PJ-Verweij/LowCostHighPrecisionPositioning---BASE2-ROVER2/SolidWorks 3D models/BASE2/Solarpanel/Base.B.solarpanel_victron_20watt.SLDASM

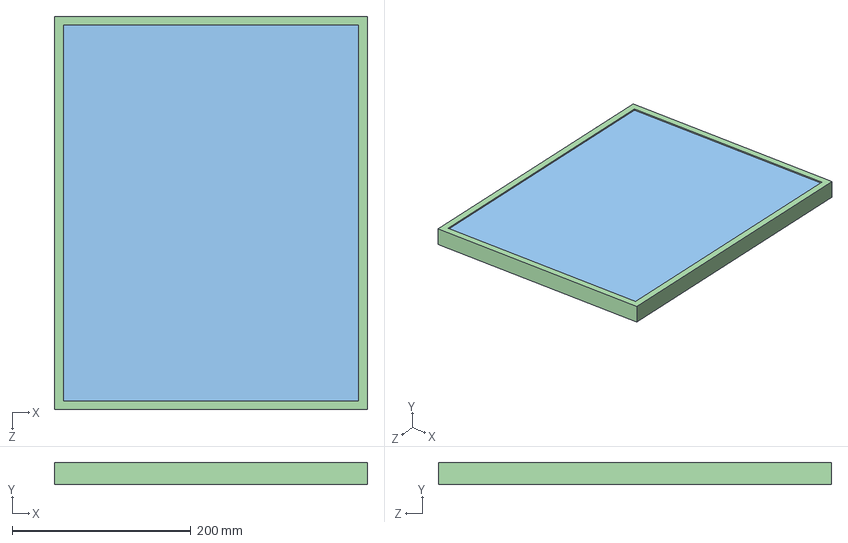
[picture p10: CAD file, 2020-09-22]
SolidWorks 3D models/BASE2/Solarpanel/Base.B.solarpanel_victron_20watt.SLDASM
350.0 x 25.0 x 440.0 mm
Solarpanel.sides
Solarpanel.glass
Solarpanel.cells
Solarpanel.backplate
