PJ-Verweij/LowCostHighPrecisionPositioning---BASE2-ROVER2/SolidWorks 3D models/BASE2/Base.Leg.Assembly.SLDASM

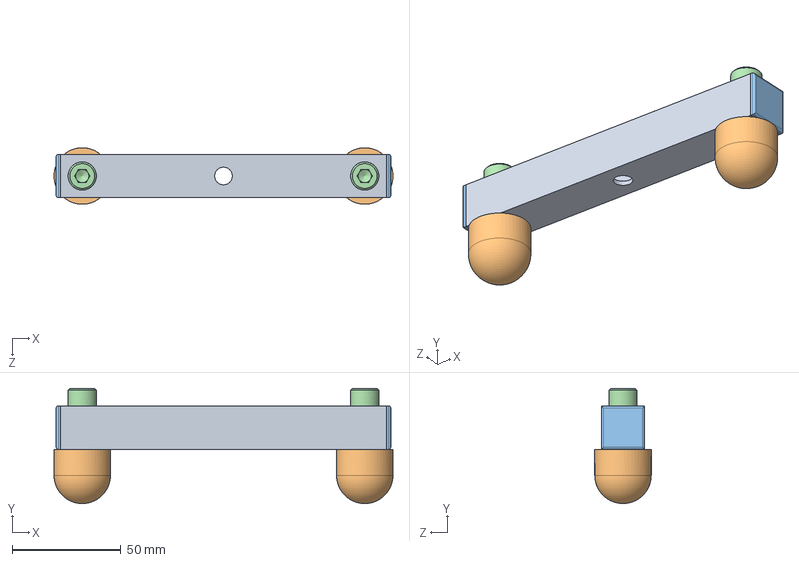
[picture p16: CAD file, 2020-09-22]
SolidWorks 3D models/BASE2/Base.Leg.Assembly.SLDASM
156.0 x 53.0 x 26.0 mm
Base.M.Square_Tube_150x20x20
Base.B.Rubber_Feet x 2
Base.B.Square_Tube_Cap x 2
socket head cap screw_am x 2
