PJ-Verweij/LowCostHighPrecisionPositioning---BASE2-ROVER2/SolidWorks 3D models/BASE2/Base.Cap.Assembly.SLDASM

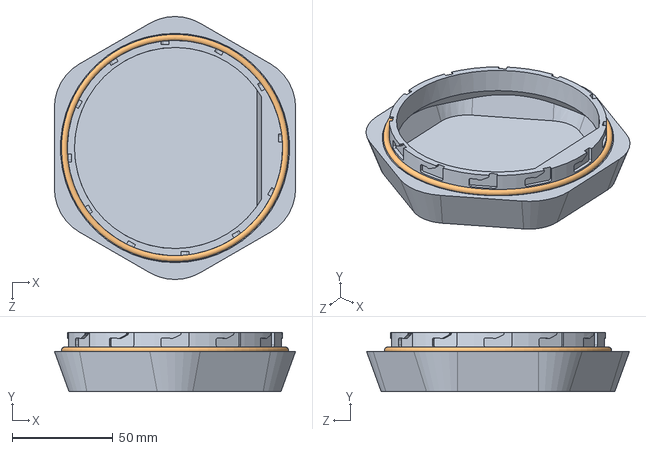
[picture p17: CAD file, 2020-09-22]
SolidWorks 3D models/BASE2/Base.Cap.Assembly.SLDASM
120.0 x 29.5 x 130.8 mm
Base.M.cap
Base.B.3x106_o-ring
