PJ-Verweij/LowCostHighPrecisionPositioning---BASE2-ROVER2/SolidWorks 3D models/BASE2/Base.Solarconnectorcap.Assembly.SLDASM

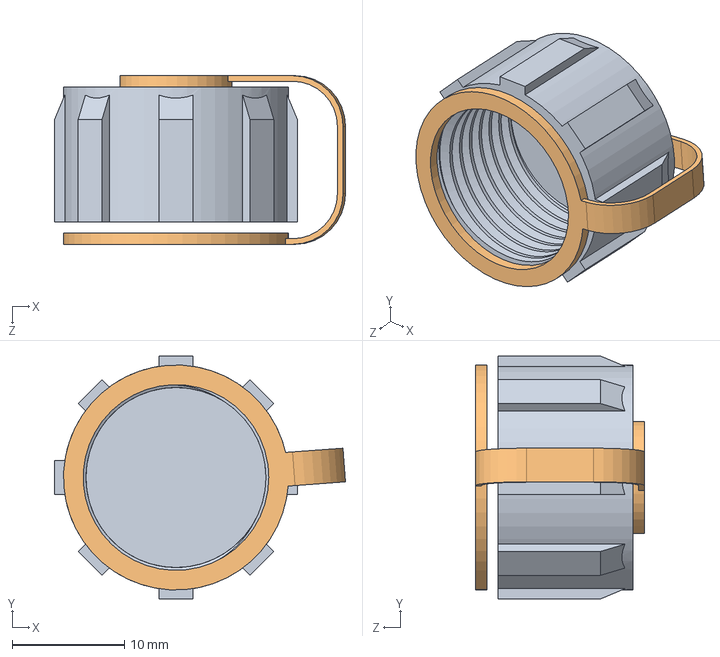
[picture p18: CAD file, 2020-09-22]
SolidWorks 3D models/BASE2/Base.Solarconnectorcap.Assembly.SLDASM
25.9 x 21.6 x 15.0 mm
Base.B.solarconnector_cap
Base.B.solarconnector_lip
