PJ-Verweij/LowCostHighPrecisionPositioning---BASE2-ROVER2/SolidWorks 3D models/BASE2/Base.B.cn3772_MPPT_regulator.SLDPRT

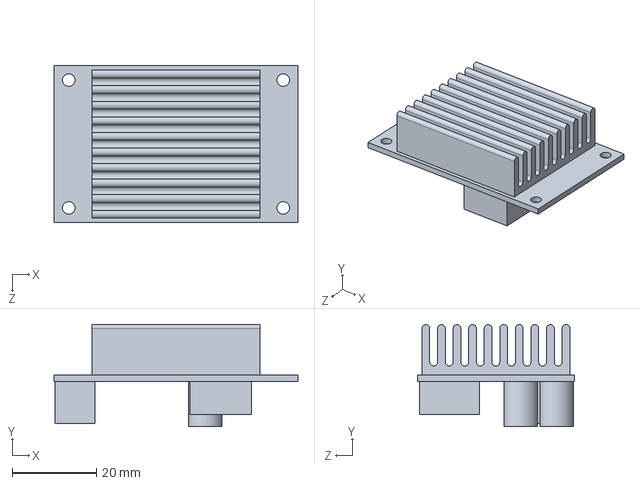
[picture p19: CAD file, 2020-09-22]
SolidWorks 3D models/BASE2/Base.B.cn3772_MPPT_regulator.SLDPRT
58.0 x 24.2 x 37.4 mm
