PJ-Verweij/LowCostHighPrecisionPositioning---BASE2-ROVER2/SolidWorks 3D models/BASE2/Solarpanel/Base.M.example_solarpanel_stand.SLDPRT

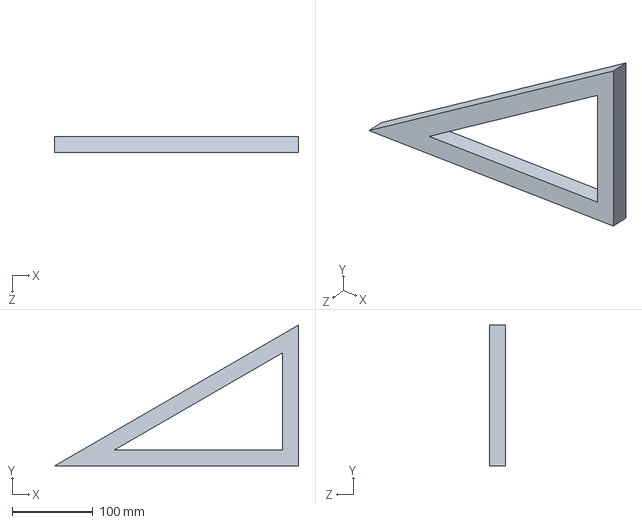
[picture p20: CAD file, 2020-09-22]
SolidWorks 3D models/BASE2/Solarpanel/Base.M.example_solarpanel_stand.SLDPRT
303.1 x 175.0 x 20.0 mm
