PJ-Verweij/LowCostHighPrecisionPositioning---BASE2-ROVER2/SolidWorks 3D models/ROVER2/Phoneholder/Rover.B.spring.SLDPRT

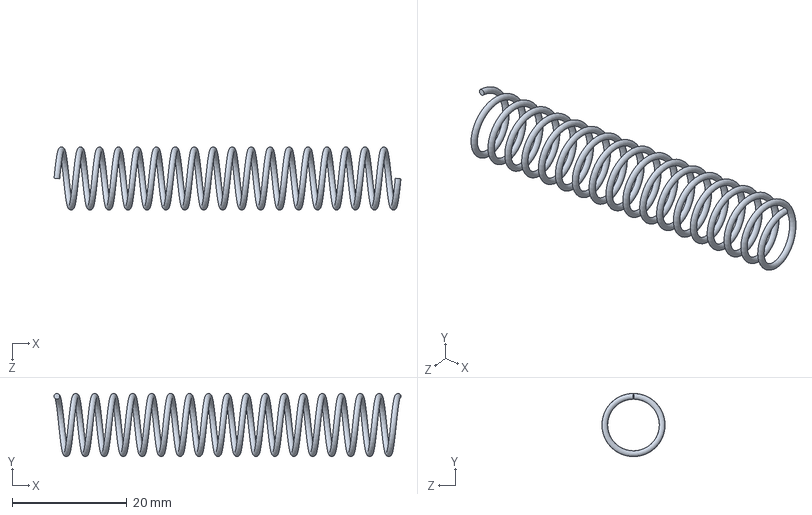
[picture p21: CAD file, 2020-09-22]
SolidWorks 3D models/ROVER2/Phoneholder/Rover.B.spring.SLDPRT
60.4 x 11.0 x 11.0 mm
