PJ-Verweij/LowCostHighPrecisionPositioning---BASE2-ROVER2/SolidWorks 3D models/ROVER2/Rover.B.18650x2_holder.SLDPRT

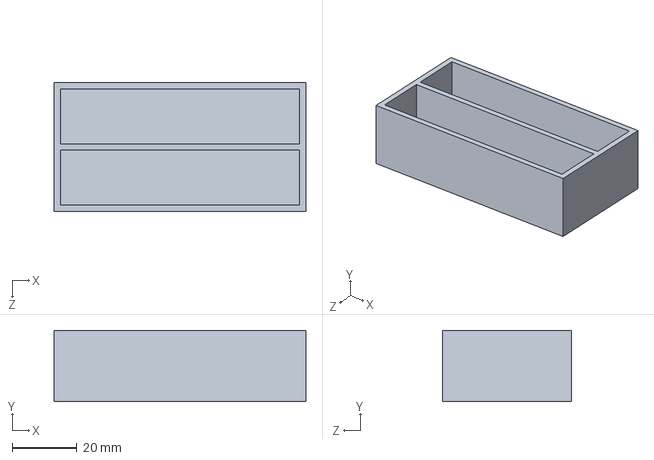
[picture p22: CAD file, 2020-09-22]
SolidWorks 3D models/ROVER2/Rover.B.18650x2_holder.SLDPRT
78.0 x 22.0 x 40.0 mm
