PJ-Verweij/LowCostHighPrecisionPositioning---BASE2-ROVER2/SolidWorks 3D models/shared parts ROVER2 and BASE2/Universal.B.Insert.5x5xm3.SLDPRT

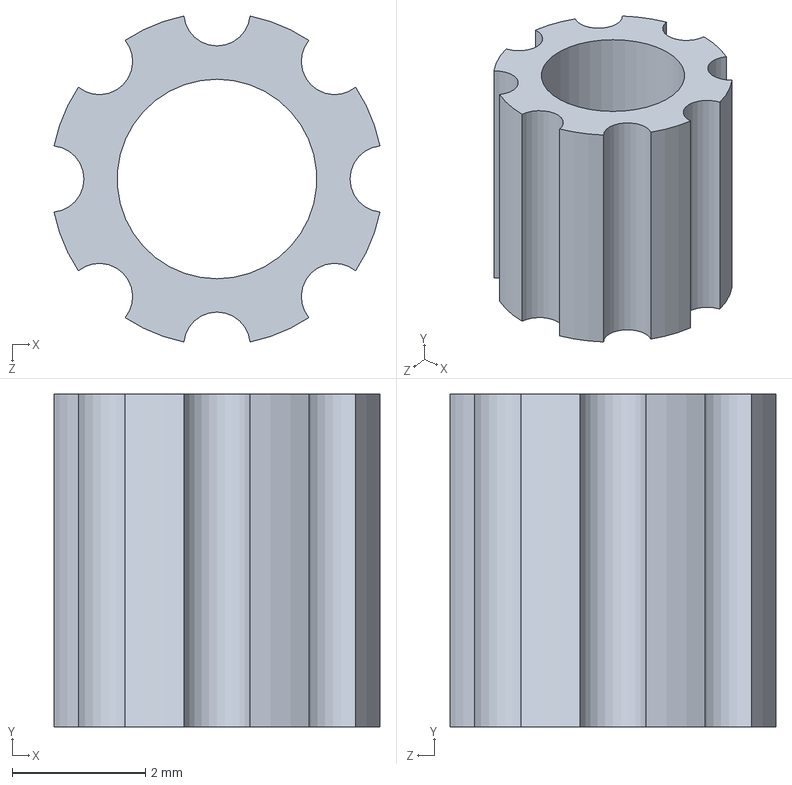
[picture p23: CAD file, 2020-09-22]
SolidWorks 3D models/shared parts ROVER2 and BASE2/Universal.B.Insert.5x5xm3.SLDPRT
4.90 x 5.00 x 4.90 mm
