PJ-Verweij/LowCostHighPrecisionPositioning---BASE2-ROVER2/SolidWorks 3D models/BASE2/Antennatop/Base.B.cellular_antenna.SLDPRT

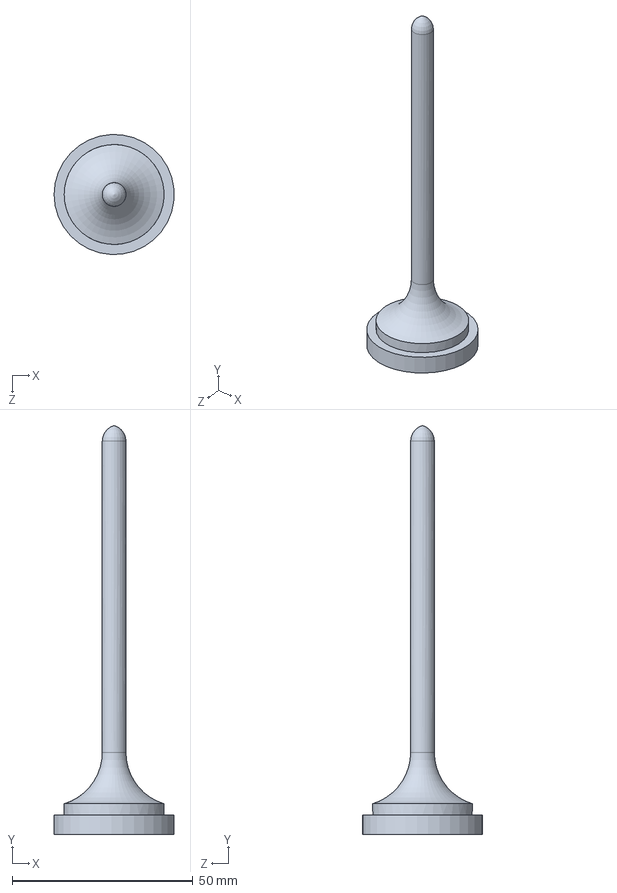
[picture p24: CAD file, 2020-09-22]
SolidWorks 3D models/BASE2/Antennatop/Base.B.cellular_antenna.SLDPRT
33.1 x 113.0 x 33.2 mm
