PJ-Verweij/LowCostHighPrecisionPositioning---BASE2-ROVER2/SolidWorks 3D models/BASE2/Base.B.solarconnector_turnablecap.SLDPRT

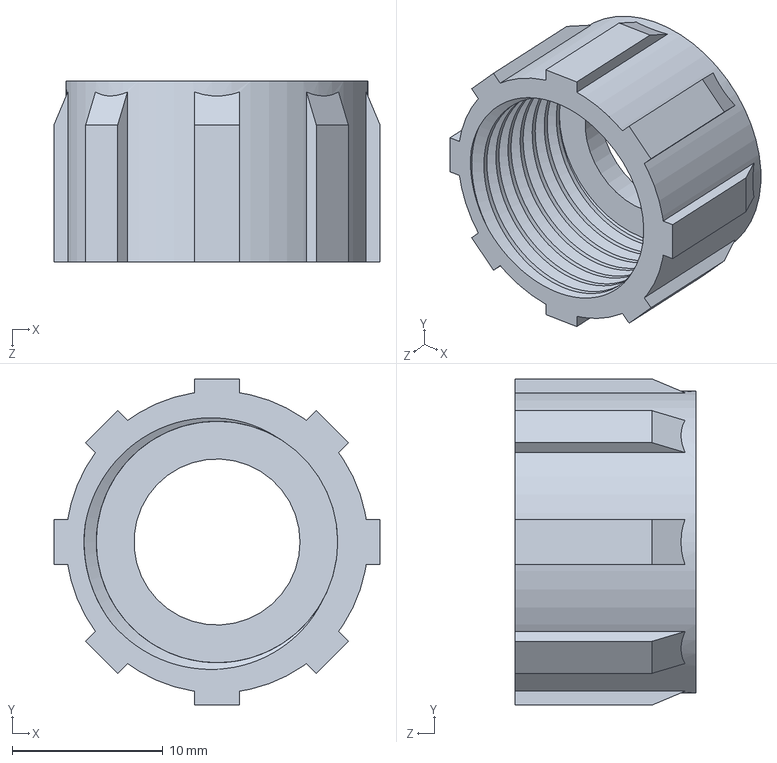
[picture p25: CAD file, 2020-09-22]
SolidWorks 3D models/BASE2/Base.B.solarconnector_turnablecap.SLDPRT
21.6 x 21.6 x 12.0 mm
