PJ-Verweij/LowCostHighPrecisionPositioning---BASE2-ROVER2/SolidWorks 3D models/BASE2/Solarpanel/Solarpanel.backplate.SLDPRT

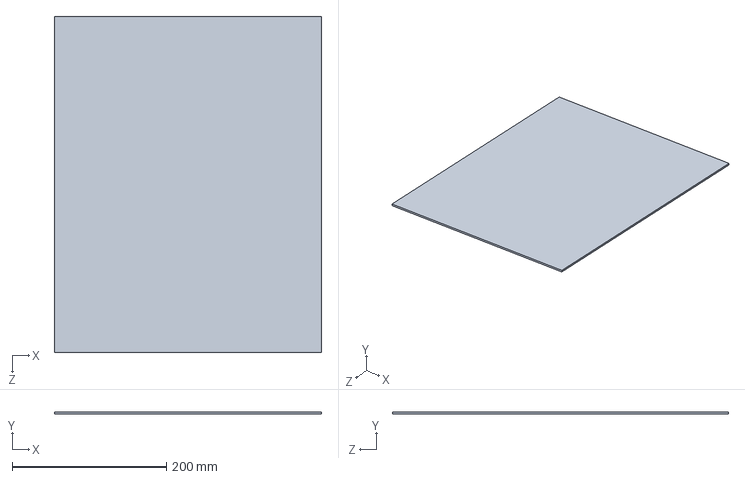
[picture p26: CAD file, 2020-09-22]
SolidWorks 3D models/BASE2/Solarpanel/Solarpanel.backplate.SLDPRT
346.0 x 3.00 x 436.0 mm
