PJ-Verweij/LowCostHighPrecisionPositioning---BASE2-ROVER2/SolidWorks 3D models/BASE2/Tripodclamp/Base.M.fixed_tripod_coupler.SLDPRT

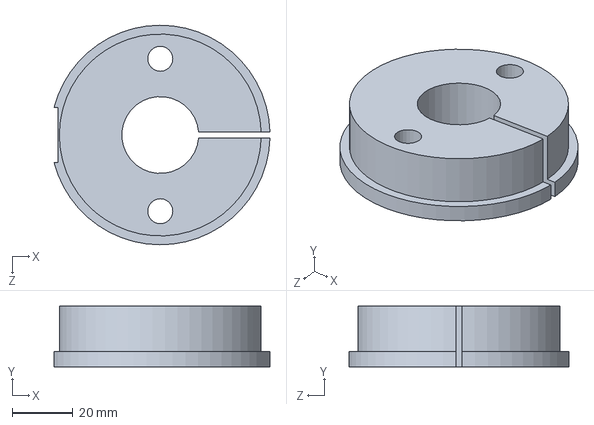
[picture p27: CAD file, 2020-09-22]
SolidWorks 3D models/BASE2/Tripodclamp/Base.M.fixed_tripod_coupler.SLDPRT
70.8 x 20.0 x 72.0 mm
