PJ-Verweij/LowCostHighPrecisionPositioning---BASE2-ROVER2/SolidWorks 3D models/ROVER2/Phoneholder/telefoonhouderbase.STL

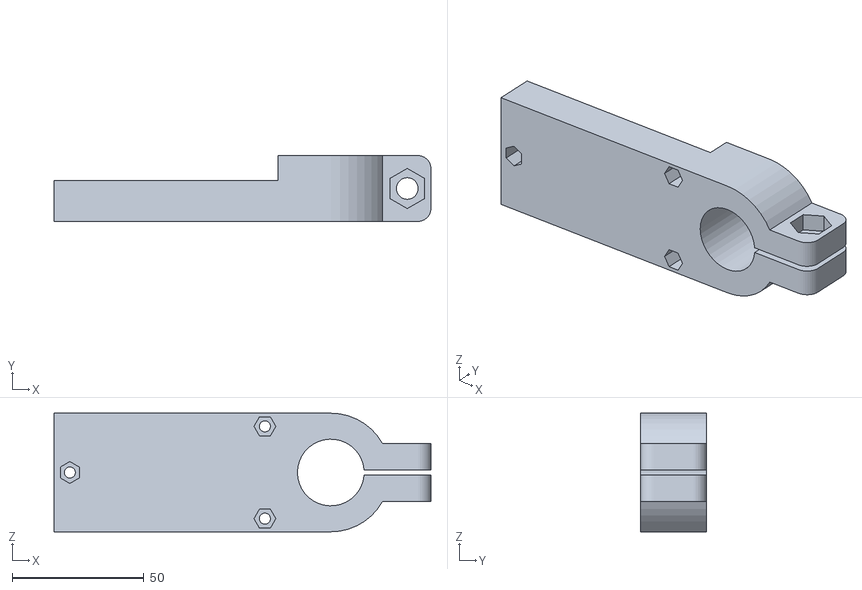
[picture p28: CAD file, 2020-09-22]
SolidWorks 3D models/ROVER2/Phoneholder/telefoonhouderbase.STL
143.0 x 25.0 x 45.0
