PJ-Verweij/LowCostHighPrecisionPositioning---BASE2-ROVER2/SolidWorks 3D models/ROVER2/Rover.M.BatteryPCB.SLDPRT

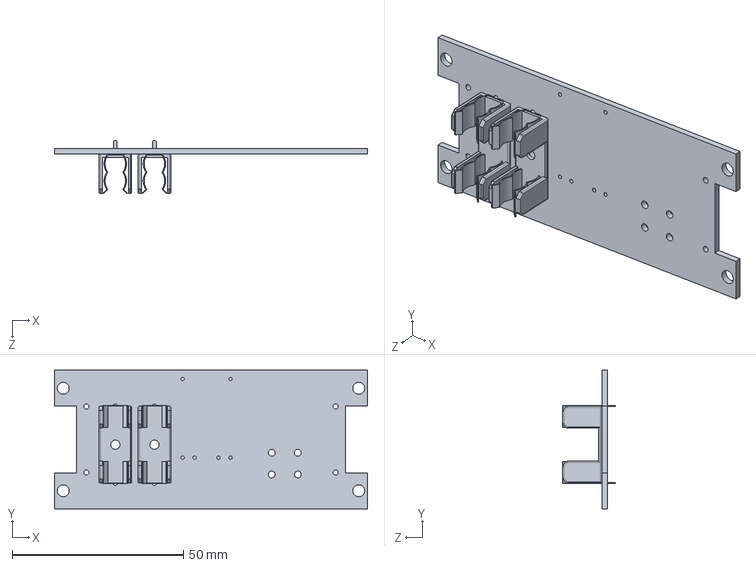
[picture p29: CAD file, 2020-09-22]
SolidWorks 3D models/ROVER2/Rover.M.BatteryPCB.SLDPRT
91.5 x 40.5 x 15.5 mm
