PJ-Verweij/LowCostHighPrecisionPositioning---BASE2-ROVER2/SolidWorks 3D models/ROVER2/Tripodclamp/Rover.M.open_tripod_coupler.SLDPRT

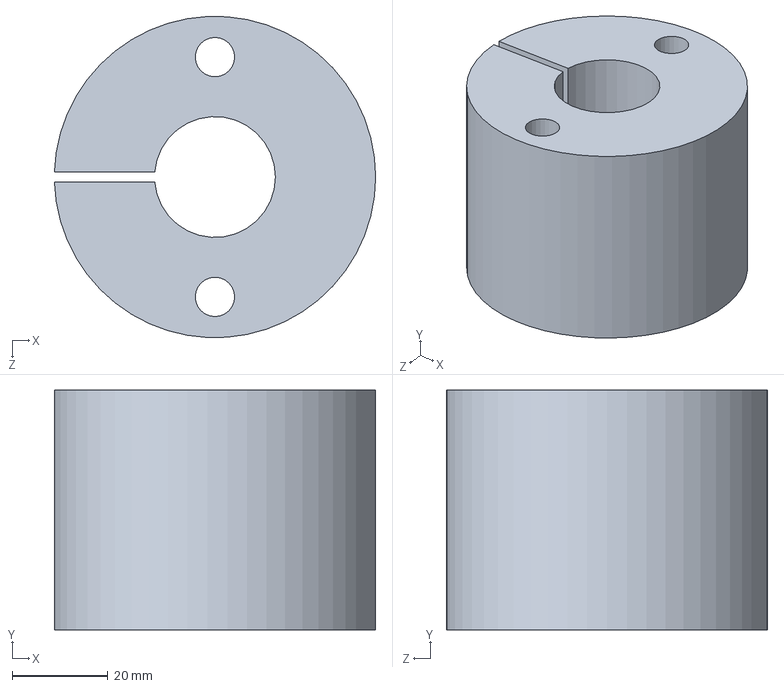
[picture p30: CAD file, 2020-09-22]
SolidWorks 3D models/ROVER2/Tripodclamp/Rover.M.open_tripod_coupler.SLDPRT
67.0 x 50.0 x 66.9 mm
