PJ-Verweij/LowCostHighPrecisionPositioning---BASE2-ROVER2/SolidWorks 3D models/shared parts ROVER2 and BASE2/Tripod/Tripodleg.hinge.SLDPRT

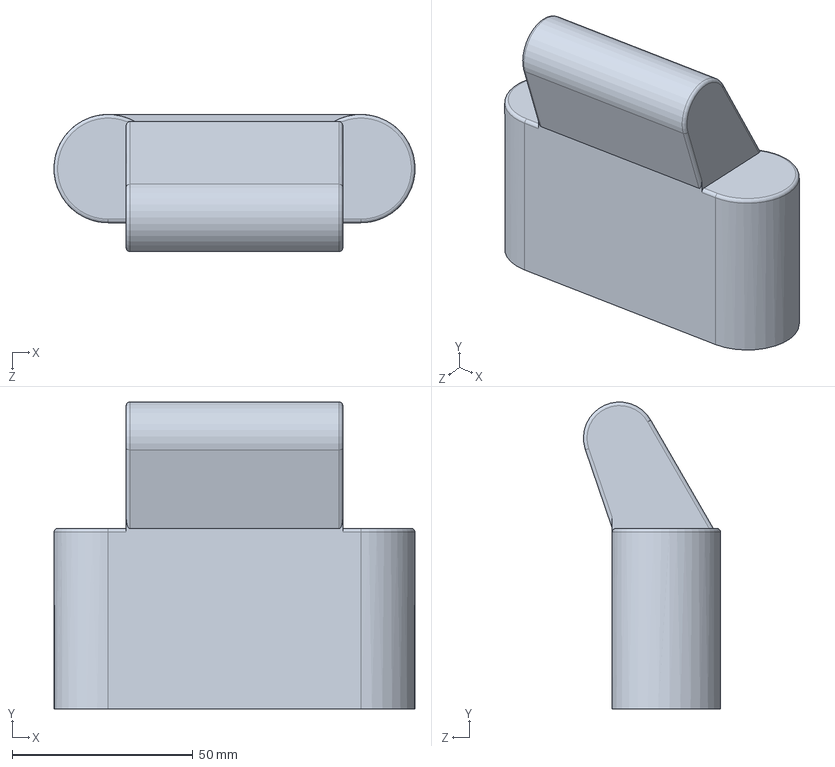
[picture p31: CAD file, 2020-09-22]
SolidWorks 3D models/shared parts ROVER2 and BASE2/Tripod/Tripodleg.hinge.SLDPRT
100.0 x 85.0 x 38.0 mm
