PJ-Verweij/LowCostHighPrecisionPositioning---BASE2-ROVER2/SolidWorks 3D models/shared parts ROVER2 and BASE2/Universal.B.knob_m8.SLDPRT

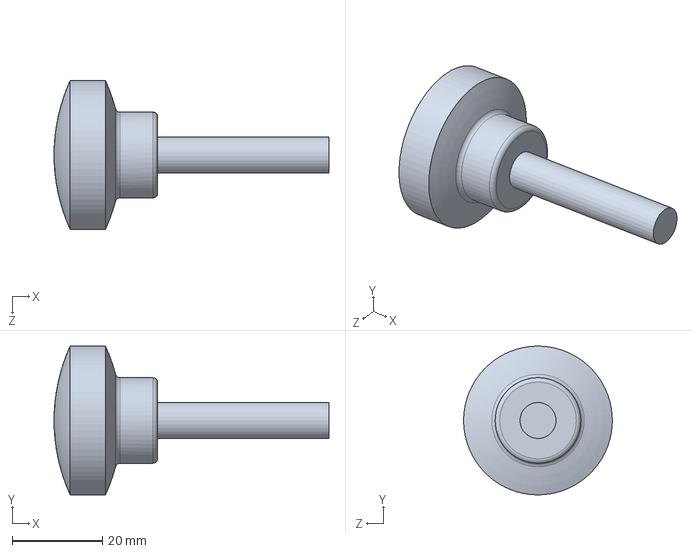
[picture p32: CAD file, 2020-09-22]
SolidWorks 3D models/shared parts ROVER2 and BASE2/Universal.B.knob_m8.SLDPRT
61.0 x 33.0 x 33.0 mm
