PJ-Verweij/LowCostHighPrecisionPositioning---BASE2-ROVER2/SolidWorks 3D models/BASE2/Antennatop/Base.M.Antennatop.SLDPRT

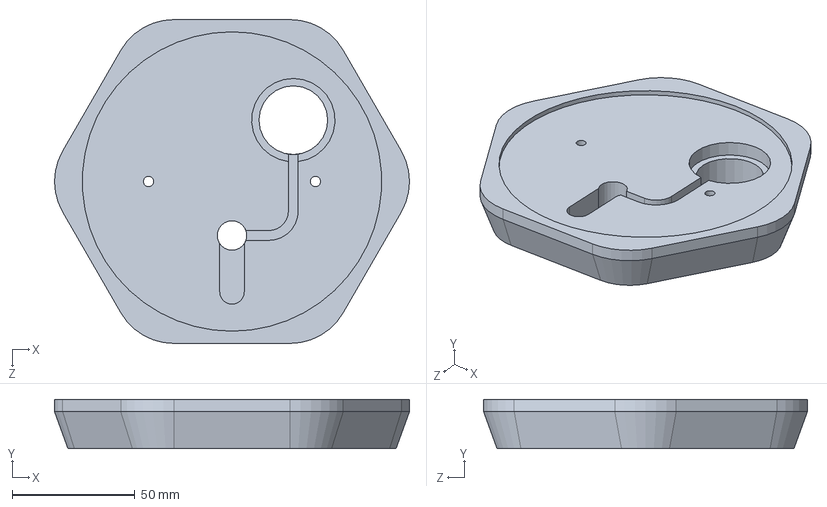
[picture p33: CAD file, 2020-09-22]
SolidWorks 3D models/BASE2/Antennatop/Base.M.Antennatop.SLDPRT
144.7 x 20.0 x 132.0 mm
