PJ-Verweij/LowCostHighPrecisionPositioning---BASE2-ROVER2/SolidWorks 3D models/BASE2/Base.B.Rubber_Feet.SLDPRT

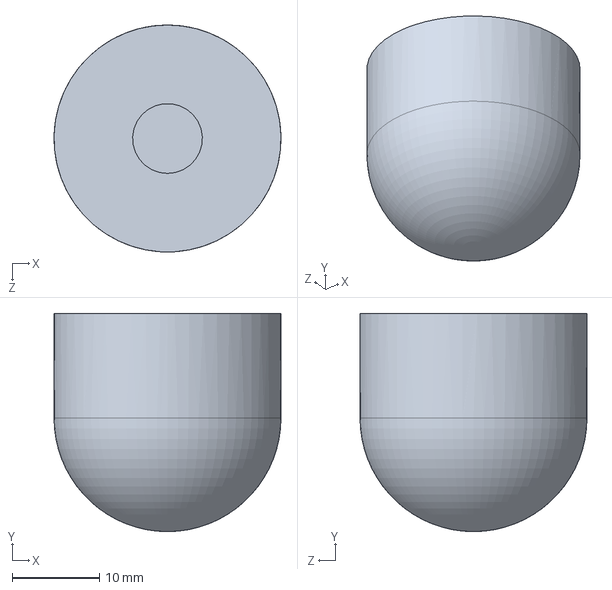
[picture p34: CAD file, 2020-09-22]
SolidWorks 3D models/BASE2/Base.B.Rubber_Feet.SLDPRT
26.0 x 25.0 x 26.0 mm
