PJ-Verweij/LowCostHighPrecisionPositioning---BASE2-ROVER2/SolidWorks 3D models/BASE2/Cable-gland-pg7-pg19/Cable Gland PG7-PG19 Body.SLDPRT

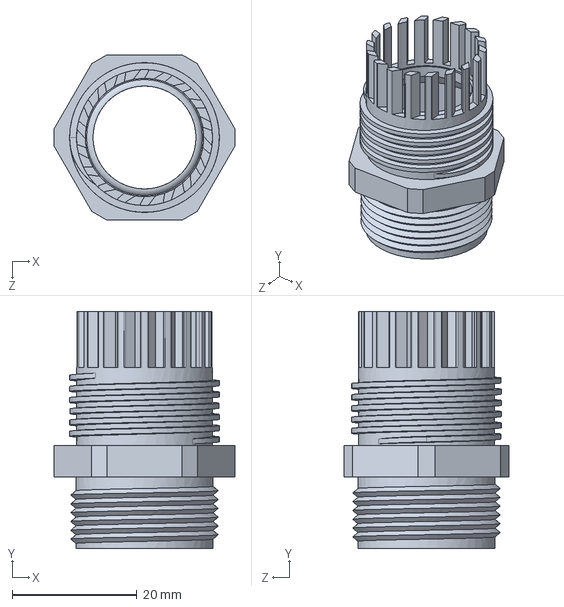
[picture p35: CAD file, 2020-09-22]
SolidWorks 3D models/BASE2/Cable-gland-pg7-pg19/Cable Gland PG7-PG19 Body.SLDPRT
29.0 x 38.0 x 26.5 mm
