PJ-Verweij/LowCostHighPrecisionPositioning---BASE2-ROVER2/SolidWorks 3D models/ROVER2/Phoneholder/Rover.M.Phoneholder_movablepart.SLDPRT

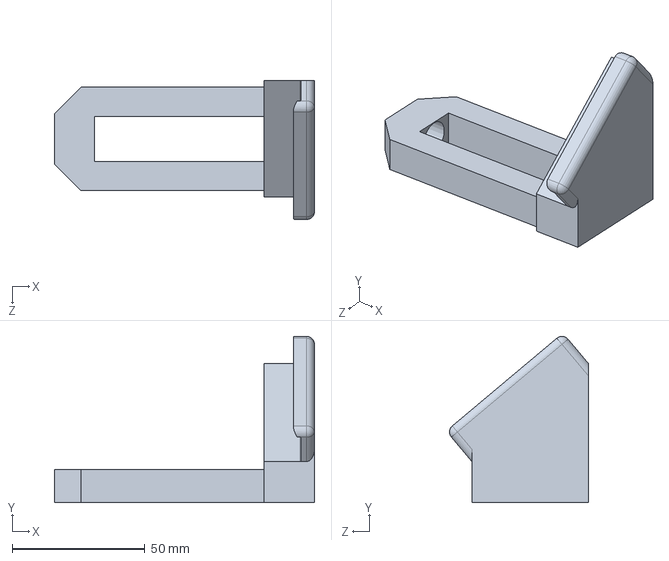
[picture p36: CAD file, 2020-09-22]
SolidWorks 3D models/ROVER2/Phoneholder/Rover.M.Phoneholder_movablepart.SLDPRT
98.0 x 62.7 x 52.4 mm
