PJ-Verweij/LowCostHighPrecisionPositioning---BASE2-ROVER2/SolidWorks 3D models/shared parts ROVER2 and BASE2/Tripod/Tripodleg.feet.SLDPRT

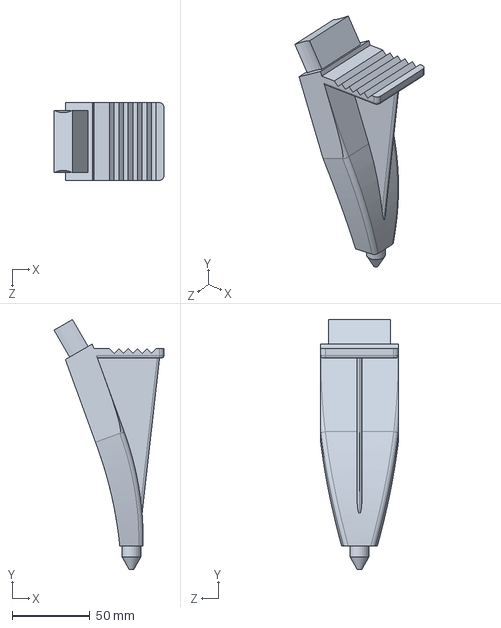
[picture p37: CAD file, 2020-09-22]
SolidWorks 3D models/shared parts ROVER2 and BASE2/Tripod/Tripodleg.feet.SLDPRT
70.7 x 160.7 x 50.0 mm
