PJ-Verweij/LowCostHighPrecisionPositioning---BASE2-ROVER2/SolidWorks 3D models/shared parts ROVER2 and BASE2/Universal.M.poleclamp.SLDPRT

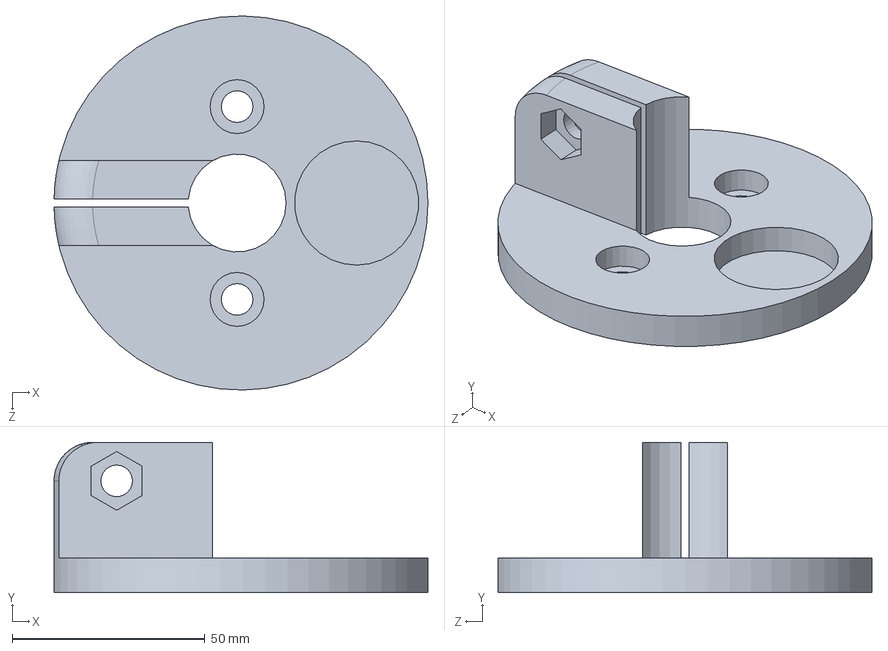
[picture p38: CAD file, 2020-09-22]
SolidWorks 3D models/shared parts ROVER2 and BASE2/Universal.M.poleclamp.SLDPRT
97.0 x 39.0 x 97.0 mm
