PJ-Verweij/LowCostHighPrecisionPositioning---BASE2-ROVER2/SolidWorks 3D models/BASE2/Base.M.Foamblockholder.SLDPRT

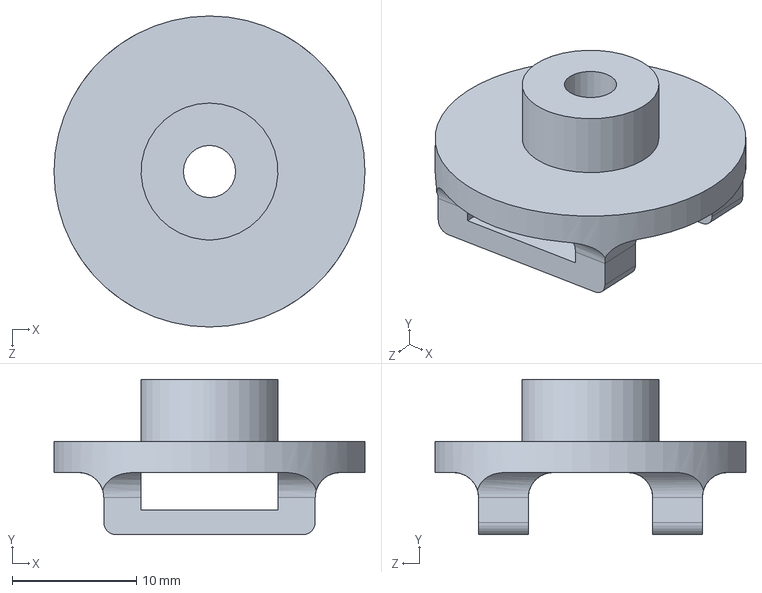
[picture p39: CAD file, 2020-09-22]
SolidWorks 3D models/BASE2/Base.M.Foamblockholder.SLDPRT
25.0 x 12.5 x 25.0 mm
