PJ-Verweij/LowCostHighPrecisionPositioning---BASE2-ROVER2/SolidWorks 3D models/BASE2/Solarpanel/Solarpanel.cells.SLDPRT

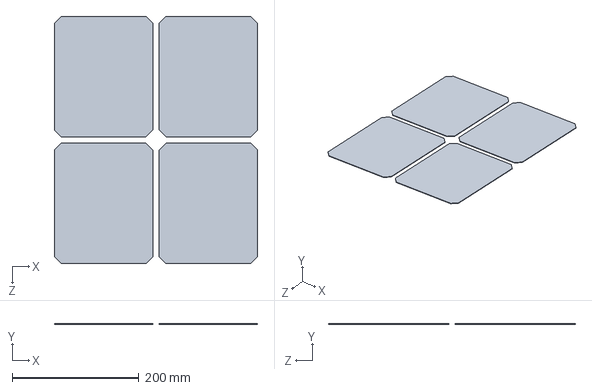
[picture p40: CAD file, 2020-09-22]
SolidWorks 3D models/BASE2/Solarpanel/Solarpanel.cells.SLDPRT
320.0 x 1.00 x 390.0 mm
