PJ-Verweij/LowCostHighPrecisionPositioning---BASE2-ROVER2/SolidWorks 3D models/ROVER2/Cable-gland-pg7-pg19/Cable Gland PG7-PG19 Sleeve.SLDPRT

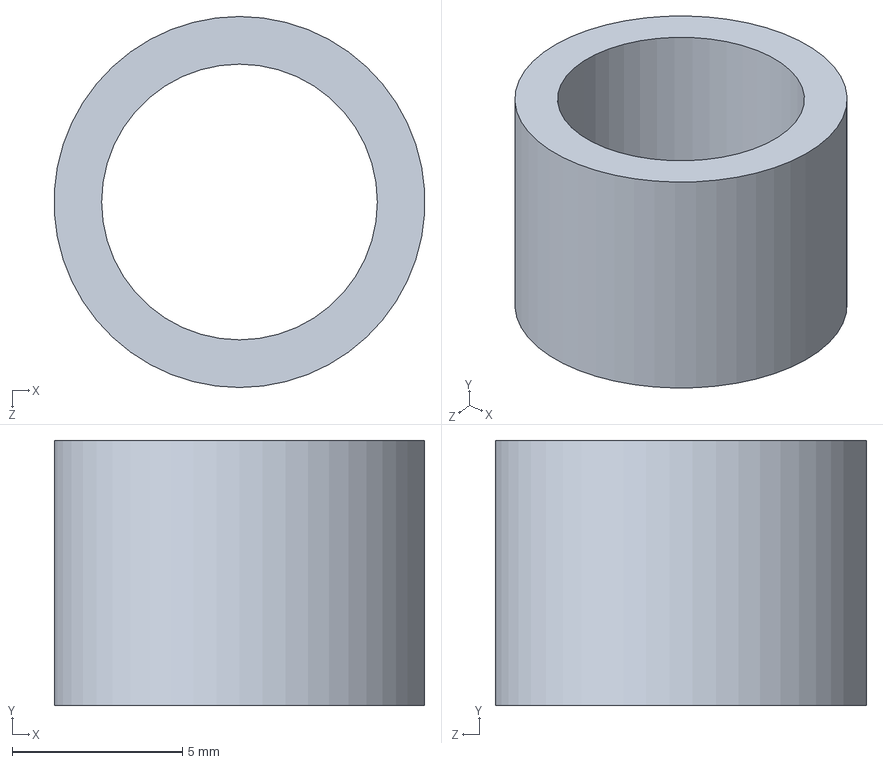
[picture p41: CAD file, 2020-09-22]
SolidWorks 3D models/ROVER2/Cable-gland-pg7-pg19/Cable Gland PG7-PG19 Sleeve.SLDPRT
10.9 x 7.80 x 10.9 mm
