PJ-Verweij/LowCostHighPrecisionPositioning---BASE2-ROVER2/SolidWorks 3D models/ROVER2/Rover.M.Lowerhousing_rubber.SLDPRT

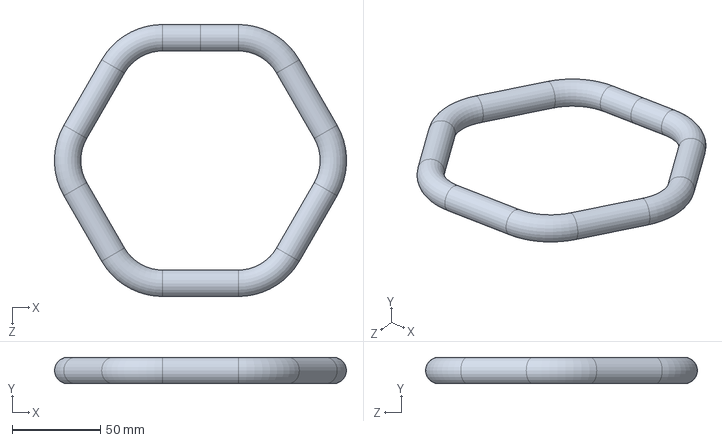
[picture p42: CAD file, 2020-09-22]
SolidWorks 3D models/ROVER2/Rover.M.Lowerhousing_rubber.SLDPRT
165.5 x 15.0 x 154.2 mm
