PJ-Verweij/LowCostHighPrecisionPositioning---BASE2-ROVER2/SolidWorks 3D models/shared parts ROVER2 and BASE2/Tripod/Tripodleg.clampclip.SLDPRT

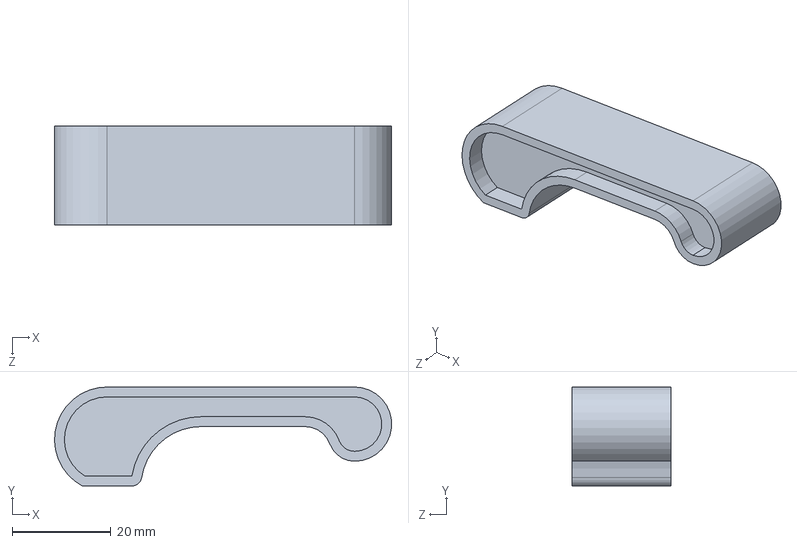
[picture p43: CAD file, 2020-09-22]
SolidWorks 3D models/shared parts ROVER2 and BASE2/Tripod/Tripodleg.clampclip.SLDPRT
68.1 x 20.0 x 20.0 mm
