PJ-Verweij/LowCostHighPrecisionPositioning---BASE2-ROVER2/SolidWorks 3D models/shared parts ROVER2 and BASE2/Universal.B.XT60E-M.SLDPRT

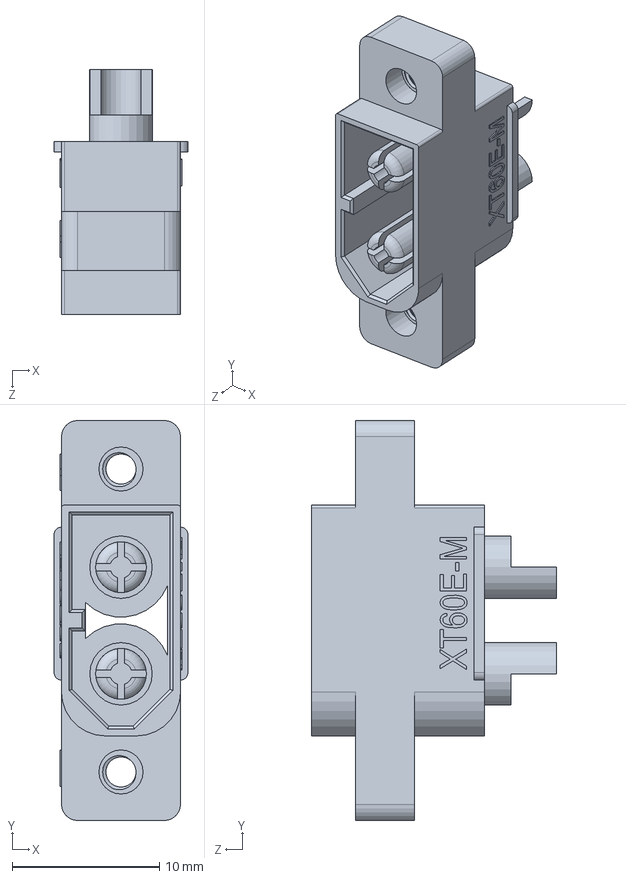
[picture p44: CAD file, 2020-09-22]
SolidWorks 3D models/shared parts ROVER2 and BASE2/Universal.B.XT60E-M.SLDPRT
9.10 x 27.2 x 16.6 mm
