PJ-Verweij/LowCostHighPrecisionPositioning---BASE2-ROVER2/SolidWorks 3D models/BASE2/Antennatop/thread adapter antenna top.SLDPRT

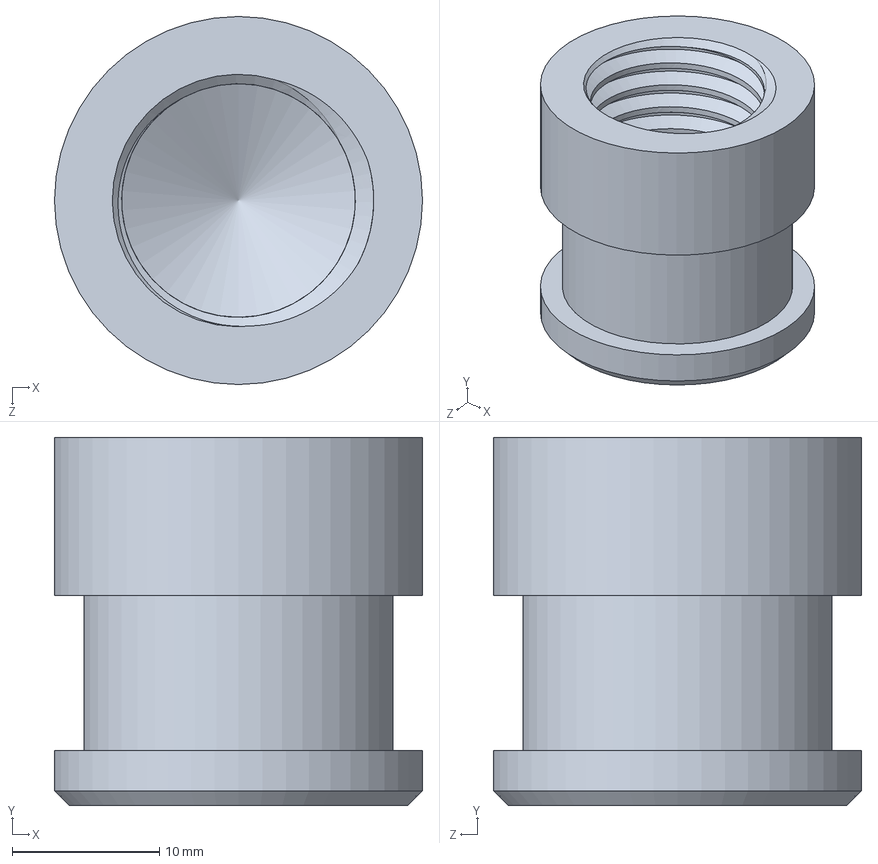
[picture p45: CAD file, 2020-09-22]
SolidWorks 3D models/BASE2/Antennatop/thread adapter antenna top.SLDPRT
25.0 x 25.0 x 25.0 mm
