PJ-Verweij/LowCostHighPrecisionPositioning---BASE2-ROVER2/SolidWorks 3D models/BASE2/Base.M.cap.SLDPRT

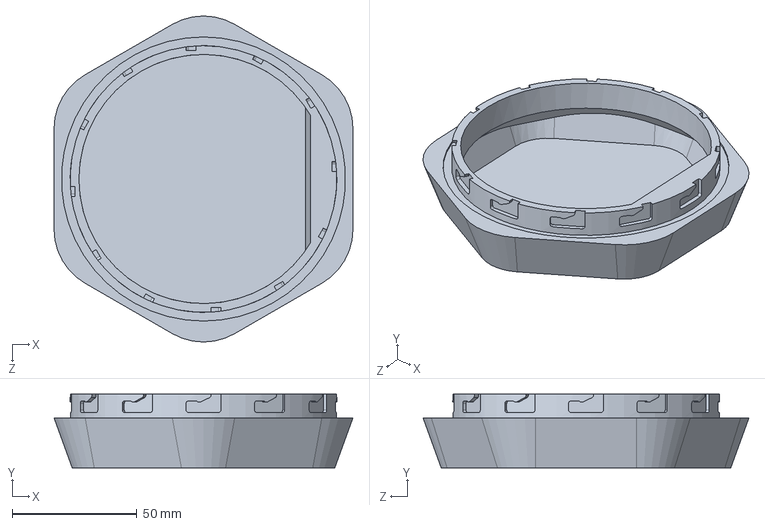
[picture p46: CAD file, 2020-09-22]
SolidWorks 3D models/BASE2/Base.M.cap.SLDPRT
120.0 x 29.5 x 130.8 mm
