PJ-Verweij/LowCostHighPrecisionPositioning---BASE2-ROVER2/SolidWorks 3D models/BASE2/Solarpanel/Solarpanel.sides.SLDPRT

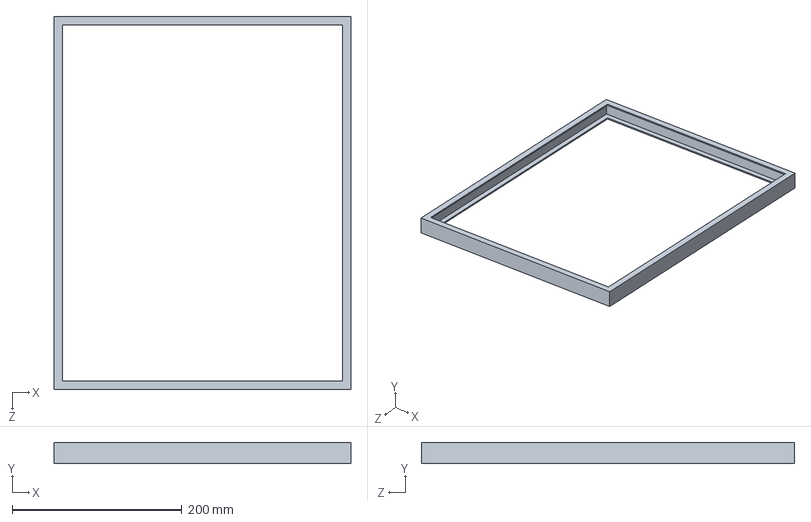
[picture p47: CAD file, 2020-09-22]
SolidWorks 3D models/BASE2/Solarpanel/Solarpanel.sides.SLDPRT
350.0 x 25.0 x 440.0 mm
