PJ-Verweij/LowCostHighPrecisionPositioning---BASE2-ROVER2/SolidWorks 3D models/ROVER2/Phoneholder/Part11.SLDPRT

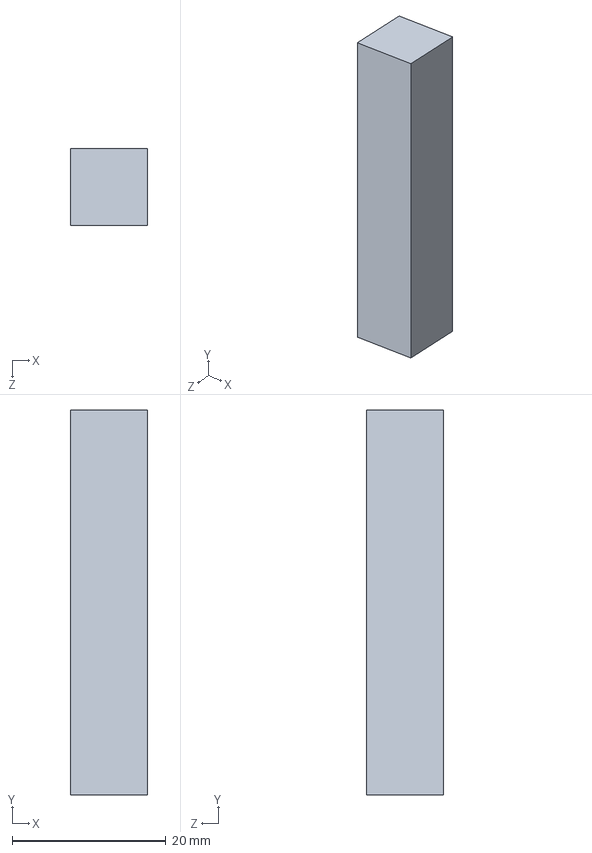
[picture p48: CAD file, 2020-09-22]
SolidWorks 3D models/ROVER2/Phoneholder/Part11.SLDPRT
10.0 x 50.0 x 10.0 mm
