PJ-Verweij/LowCostHighPrecisionPositioning---BASE2-ROVER2/SolidWorks 3D models/ROVER2/Rover.B.regular_usb_breakout.SLDPRT

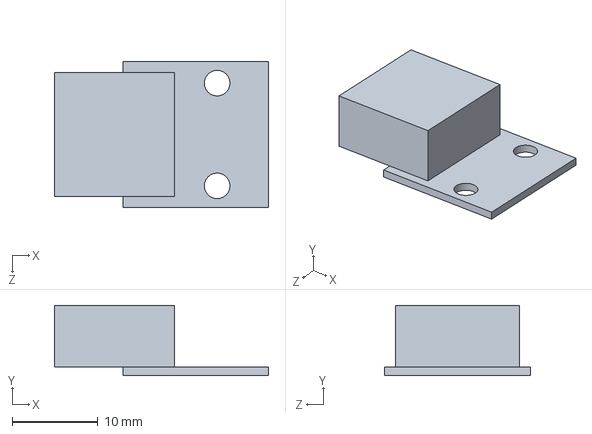
[picture p49: CAD file, 2020-09-22]
SolidWorks 3D models/ROVER2/Rover.B.regular_usb_breakout.SLDPRT
25.0 x 8.20 x 17.0 mm
