PJ-Verweij/LowCostHighPrecisionPositioning---BASE2-ROVER2/SolidWorks 3D models/shared parts ROVER2 and BASE2/Universal.B.level_32mm.SLDPRT

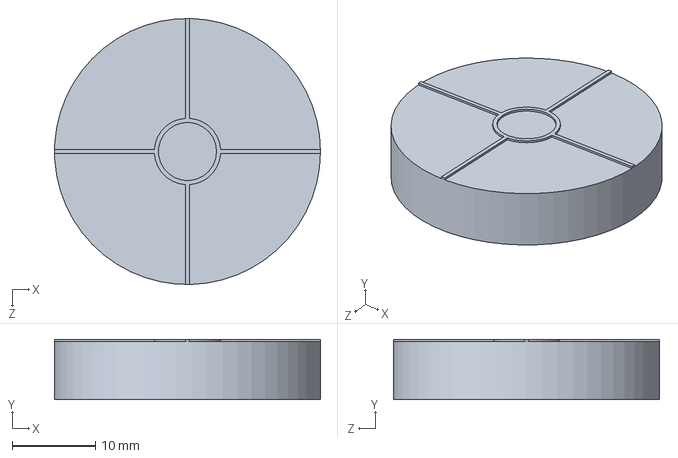
[picture p50: CAD file, 2020-09-22]
SolidWorks 3D models/shared parts ROVER2 and BASE2/Universal.B.level_32mm.SLDPRT
32.0 x 7.25 x 32.0 mm
