PJ-Verweij/LowCostHighPrecisionPositioning---BASE2-ROVER2/SolidWorks 3D models/BASE2/Base.B.solarconnector_cablegland.SLDPRT

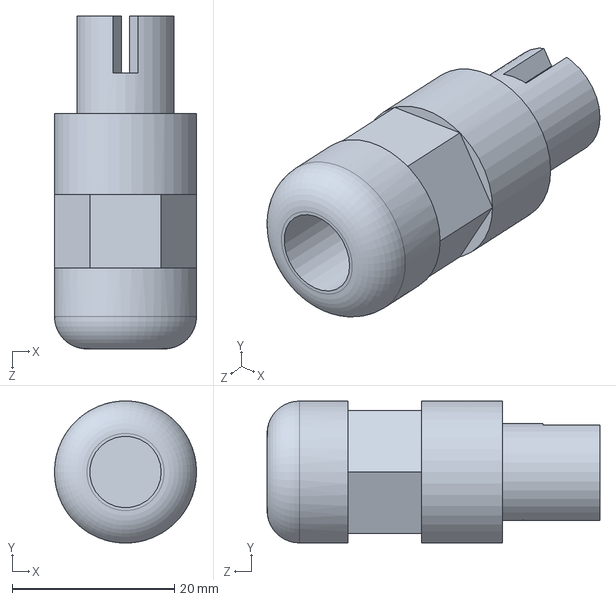
[picture p51: CAD file, 2020-09-22]
SolidWorks 3D models/BASE2/Base.B.solarconnector_cablegland.SLDPRT
17.5 x 17.5 x 41.0 mm
