PJ-Verweij/LowCostHighPrecisionPositioning---BASE2-ROVER2/SolidWorks 3D models/ROVER2/Phoneholder/Rover.M.Phoneholder_toppart.SLDPRT

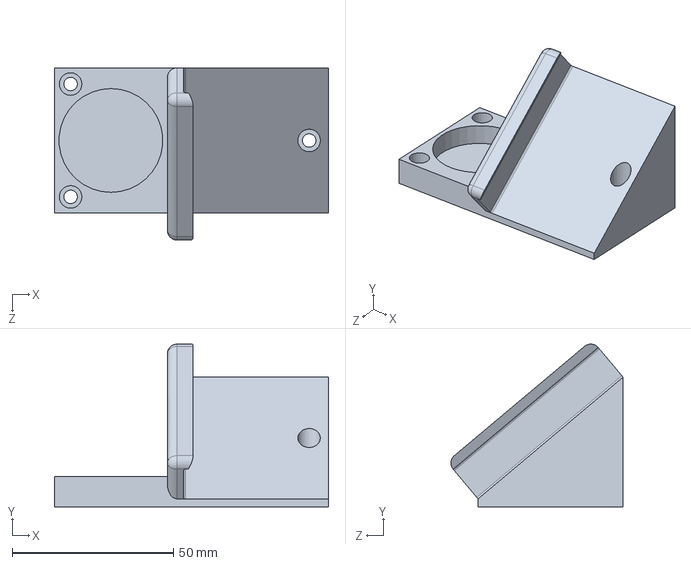
[picture p52: CAD file, 2020-09-22]
SolidWorks 3D models/ROVER2/Phoneholder/Rover.M.Phoneholder_toppart.SLDPRT
85.0 x 50.5 x 53.4 mm
