PJ-Verweij/LowCostHighPrecisionPositioning---BASE2-ROVER2/SolidWorks 3D models/ROVER2/Rover.M.cap.SLDPRT

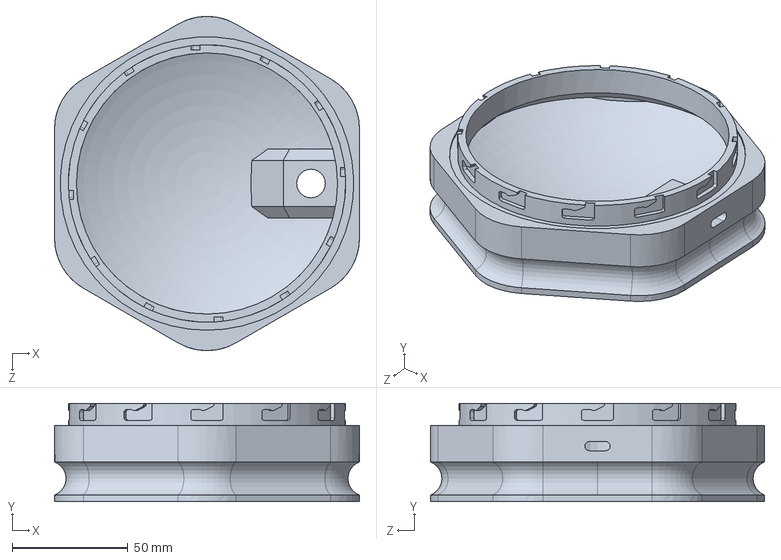
[picture p53: CAD file, 2020-09-22]
SolidWorks 3D models/ROVER2/Rover.M.cap.SLDPRT
132.0 x 42.5 x 144.7 mm
