PJ-Verweij/LowCostHighPrecisionPositioning---BASE2-ROVER2/SolidWorks 3D models/shared parts ROVER2 and BASE2/Tripod/Tripodleg.tube.SLDPRT

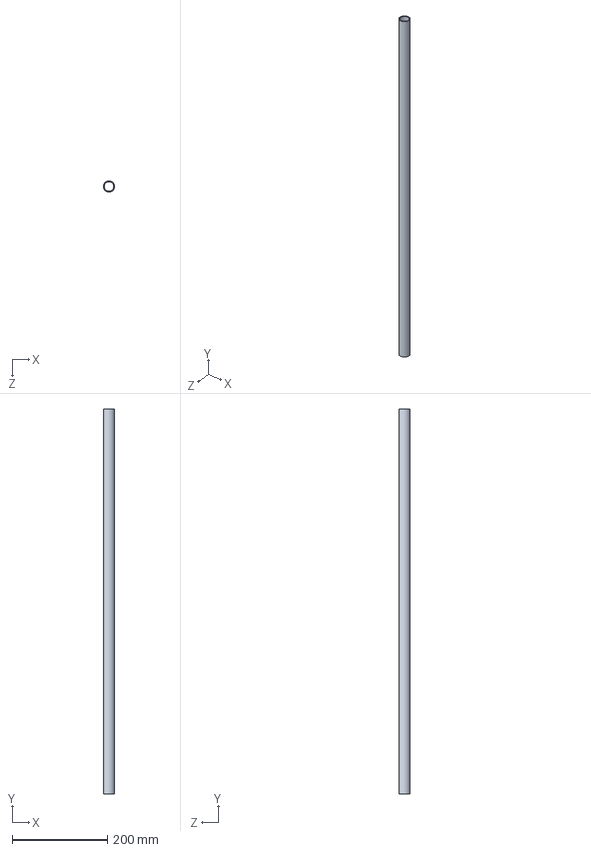
[picture p54: CAD file, 2020-09-22]
SolidWorks 3D models/shared parts ROVER2 and BASE2/Tripod/Tripodleg.tube.SLDPRT
24.0 x 810.0 x 24.0 mm
