PJ-Verweij/LowCostHighPrecisionPositioning---BASE2-ROVER2/SolidWorks 3D models/shared parts ROVER2 and BASE2/Universal.B.IP65_rockerswitch_R1366A802.SLDPRT

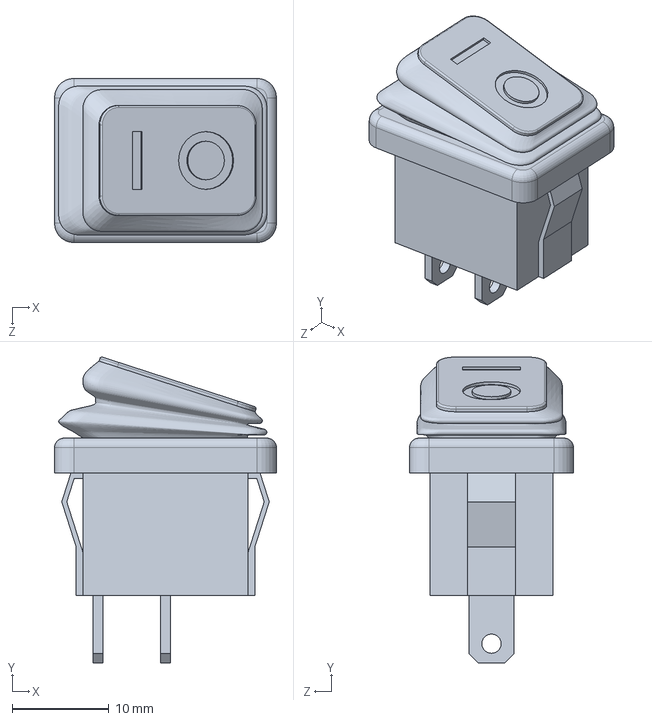
[picture p55: CAD file, 2020-09-22]
SolidWorks 3D models/shared parts ROVER2 and BASE2/Universal.B.IP65_rockerswitch_R1366A802.SLDPRT
23.0 x 31.7 x 17.0 mm
