PJ-Verweij/LowCostHighPrecisionPositioning---BASE2-ROVER2/SolidWorks 3D models/BASE2/Base.M.Square_Tube_150x20x20.SLDPRT

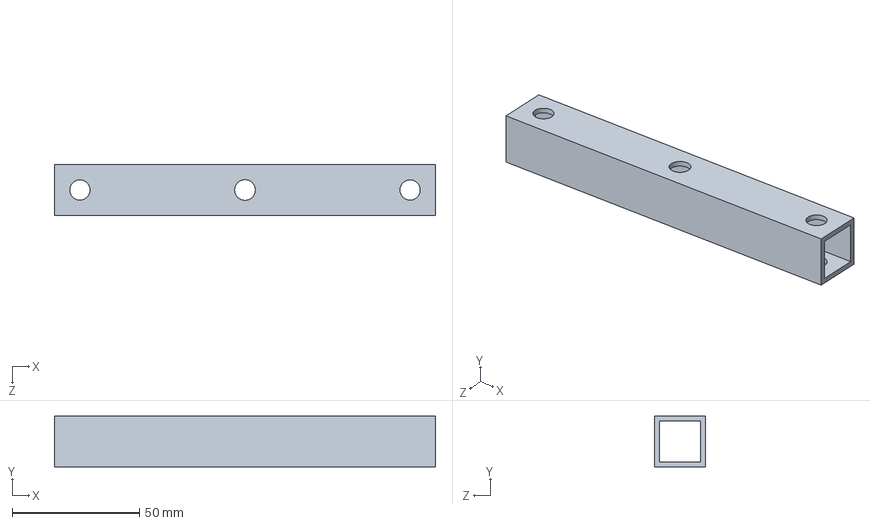
[picture p56: CAD file, 2020-09-22]
SolidWorks 3D models/BASE2/Base.M.Square_Tube_150x20x20.SLDPRT
150.0 x 20.0 x 20.0 mm
