PJ-Verweij/LowCostHighPrecisionPositioning---BASE2-ROVER2/SolidWorks 3D models/BASE2/Solarpanel/frame.SLDPRT

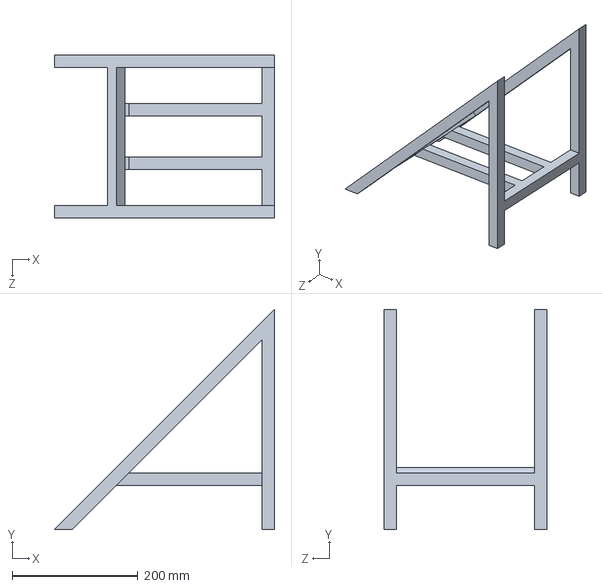
[picture p57: CAD file, 2020-09-22]
SolidWorks 3D models/BASE2/Solarpanel/frame.SLDPRT
350.0 x 350.0 x 260.0 mm
