PJ-Verweij/LowCostHighPrecisionPositioning---BASE2-ROVER2/SolidWorks 3D models/ROVER2/Rover.M.RoverPCB.SLDPRT

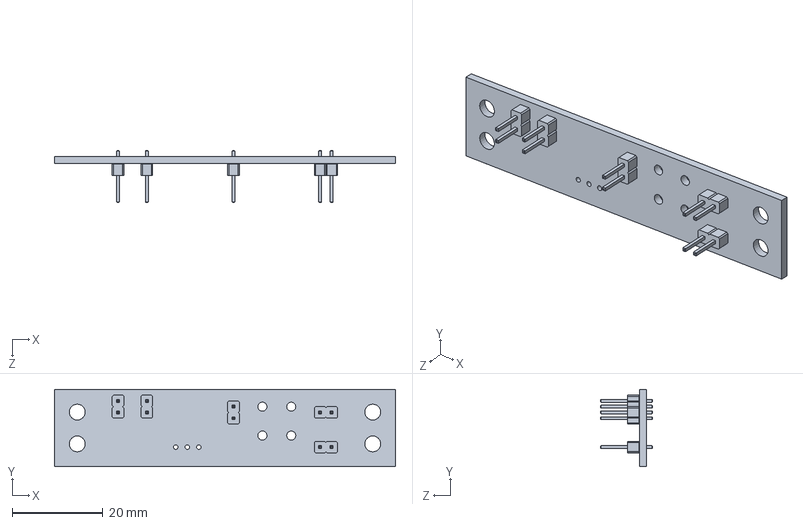
[picture p58: CAD file, 2020-09-22]
SolidWorks 3D models/ROVER2/Rover.M.RoverPCB.SLDPRT
75.0 x 17.0 x 11.5 mm
