PJ-Verweij/LowCostHighPrecisionPositioning---BASE2-ROVER2/SolidWorks 3D models/shared parts ROVER2 and BASE2/Tripod/Tripodleg.lower_guide.SLDPRT

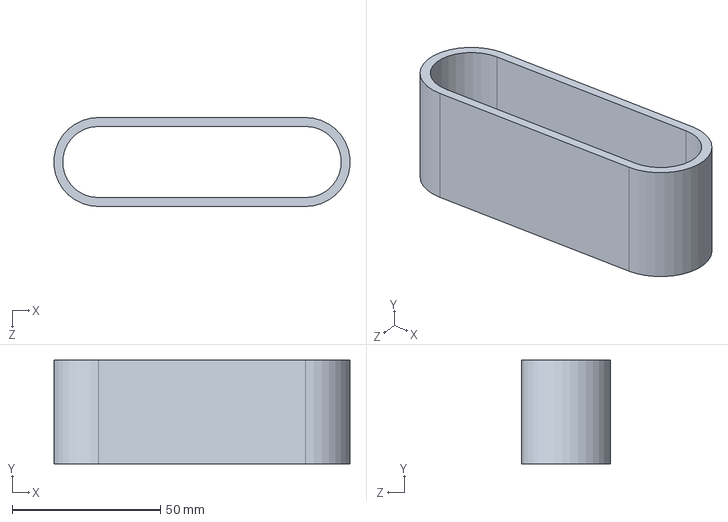
[picture p59: CAD file, 2020-09-22]
SolidWorks 3D models/shared parts ROVER2 and BASE2/Tripod/Tripodleg.lower_guide.SLDPRT
99.9 x 35.0 x 30.0 mm
