PJ-Verweij/LowCostHighPrecisionPositioning---BASE2-ROVER2/SolidWorks 3D models/shared parts ROVER2 and BASE2/Universal.B.Foamblock_STEGO.SLDPRT

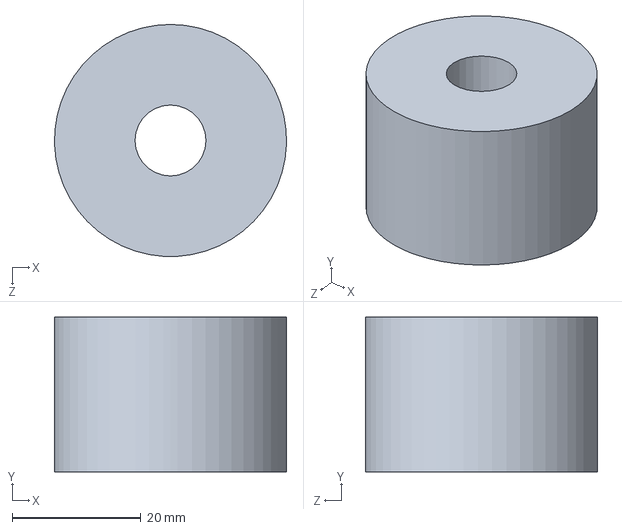
[picture p60: CAD file, 2020-09-22]
SolidWorks 3D models/shared parts ROVER2 and BASE2/Universal.B.Foamblock_STEGO.SLDPRT
36.0 x 24.0 x 36.0 mm
