PJ-Verweij/LowCostHighPrecisionPositioning---BASE2-ROVER2/SolidWorks 3D models/BASE2/Base.M.BasePCB.SLDPRT

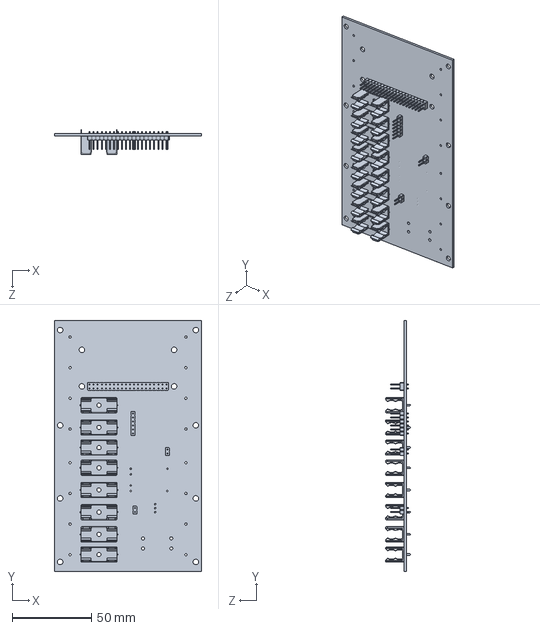
[picture p61: CAD file, 2020-09-22]
SolidWorks 3D models/BASE2/Base.M.BasePCB.SLDPRT
92.8 x 158.0 x 15.5 mm
