PJ-Verweij/LowCostHighPrecisionPositioning---BASE2-ROVER2/SolidWorks 3D models/ROVER2/Rover.M.Lowerhousing.SLDPRT

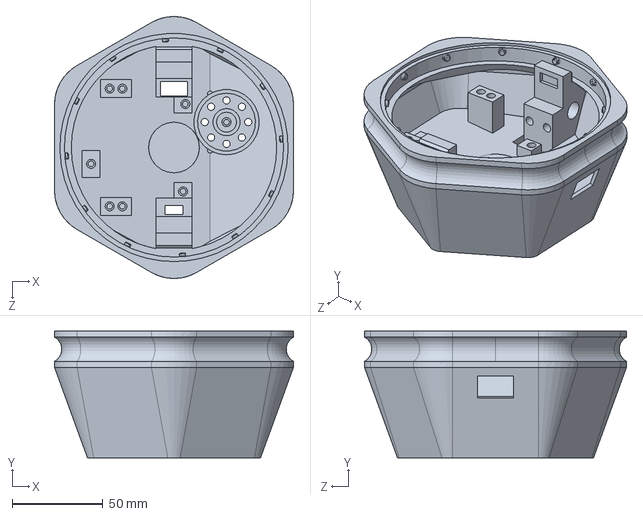
[picture p62: CAD file, 2020-09-22]
SolidWorks 3D models/ROVER2/Rover.M.Lowerhousing.SLDPRT
132.0 x 70.0 x 144.7 mm
