PJ-Verweij/LowCostHighPrecisionPositioning---BASE2-ROVER2/SolidWorks 3D models/shared parts ROVER2 and BASE2/Tripod/Tripod.baseplate.SLDPRT

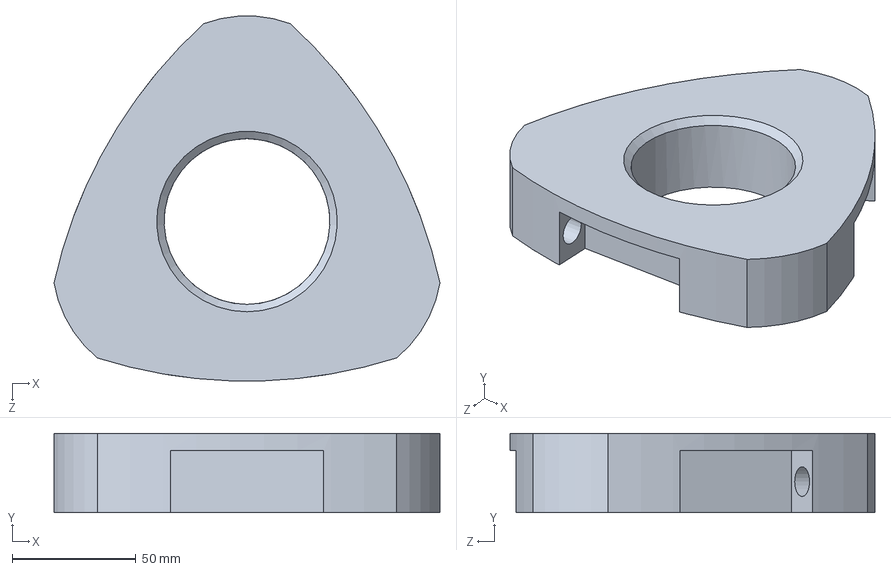
[picture p63: CAD file, 2020-09-22]
SolidWorks 3D models/shared parts ROVER2 and BASE2/Tripod/Tripod.baseplate.SLDPRT
156.1 x 32.0 x 147.5 mm
