PJ-Verweij/LowCostHighPrecisionPositioning---BASE2-ROVER2/SolidWorks 3D models/shared parts ROVER2 and BASE2/Universal.B.U3V12F5.SLDPRT

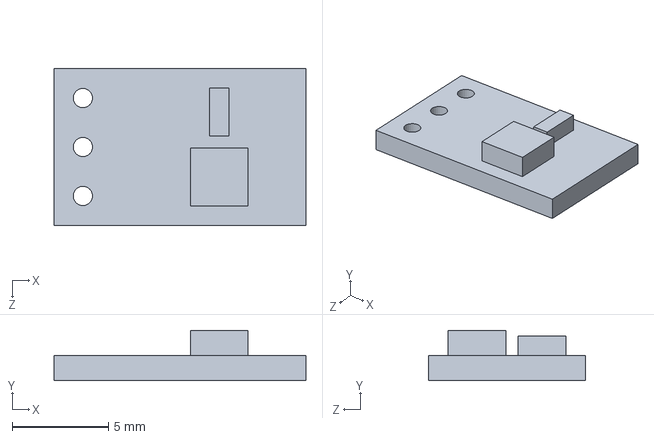
[picture p64: CAD file, 2020-09-22]
SolidWorks 3D models/shared parts ROVER2 and BASE2/Universal.B.U3V12F5.SLDPRT
13.1 x 2.60 x 8.13 mm
