PJ-Verweij/LowCostHighPrecisionPositioning---BASE2-ROVER2/SolidWorks 3D models/BASE2/Base.M.rails_left.SLDPRT

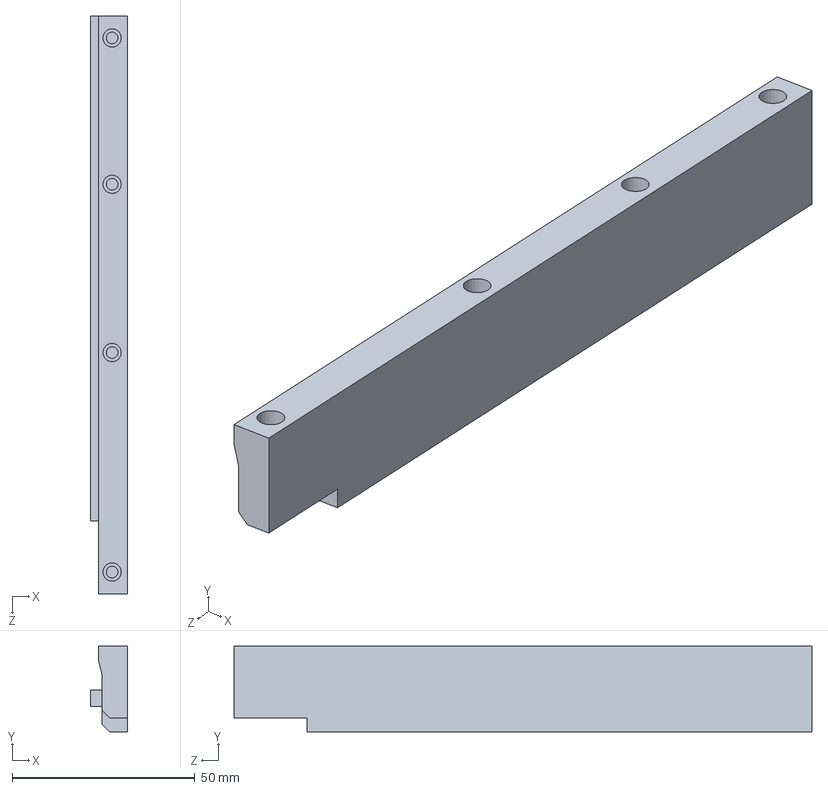
[picture p65: CAD file, 2020-09-22]
SolidWorks 3D models/BASE2/Base.M.rails_left.SLDPRT
10.1 x 23.5 x 158.0 mm
