PJ-Verweij/LowCostHighPrecisionPositioning---BASE2-ROVER2/SolidWorks 3D models/ROVER2/Rover.M.Batteryhousing.SLDPRT

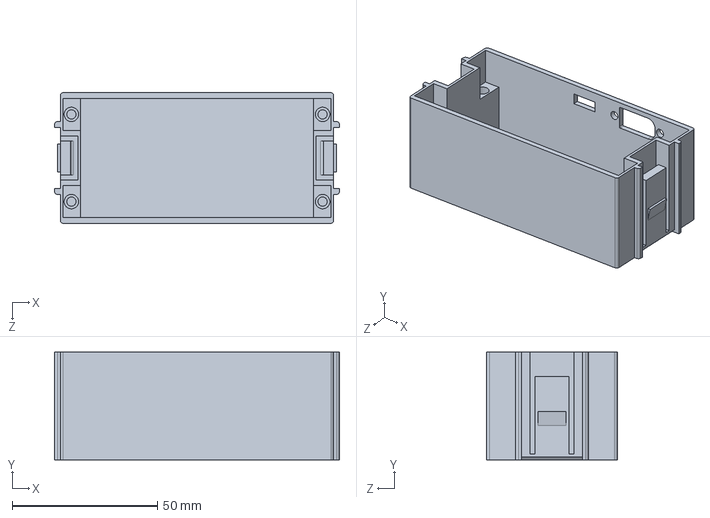
[picture p66: CAD file, 2020-09-22]
SolidWorks 3D models/ROVER2/Rover.M.Batteryhousing.SLDPRT
98.0 x 37.0 x 45.0 mm
