PJ-Verweij/LowCostHighPrecisionPositioning---BASE2-ROVER2/SolidWorks 3D models/ROVER2/Rover.B.micro_usb_breakout.SLDPRT

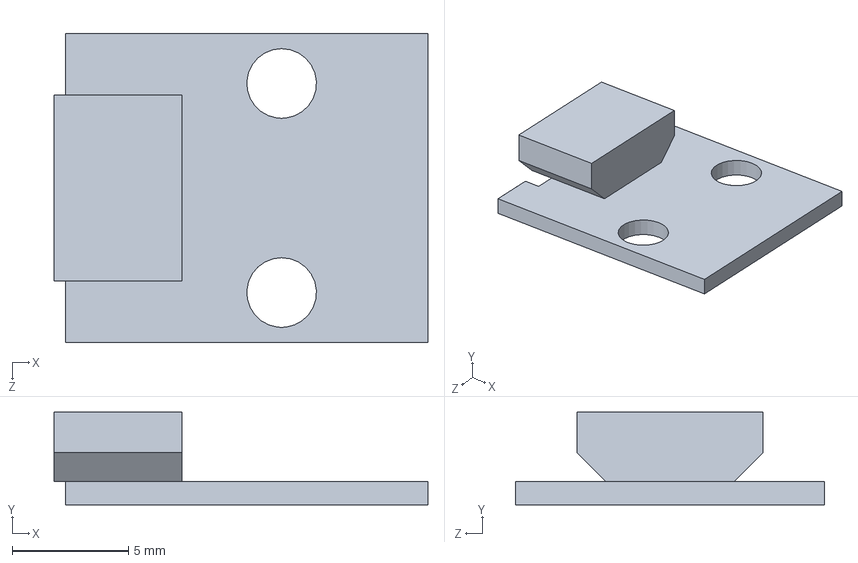
[picture p70: CAD file, 2020-09-22]
SolidWorks 3D models/ROVER2/Rover.B.micro_usb_breakout.SLDPRT
16.1 x 4.00 x 13.3 mm
