PJ-Verweij/LowCostHighPrecisionPositioning---BASE2-ROVER2/SolidWorks 3D models/BASE2/Base.B.3x106_o-ring.SLDPRT

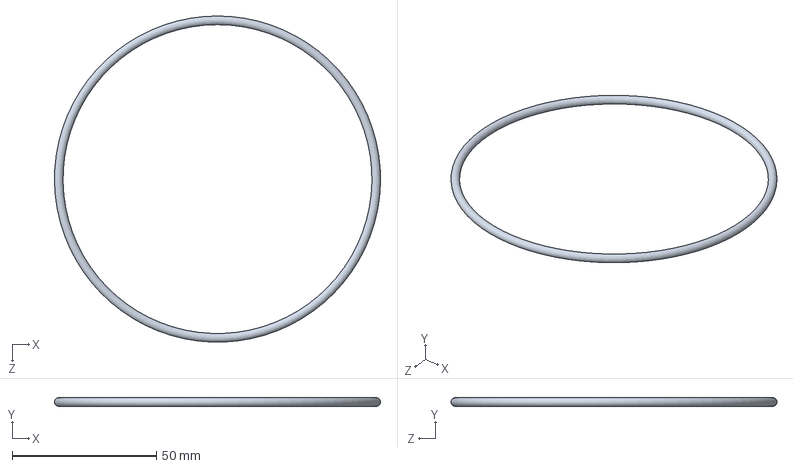
[picture p73: CAD file, 2020-09-22]
SolidWorks 3D models/BASE2/Base.B.3x106_o-ring.SLDPRT
113.0 x 3.00 x 113.0 mm
