PJ-Verweij/LowCostHighPrecisionPositioning---BASE2-ROVER2/SolidWorks 3D models/shared parts ROVER2 and BASE2/Universal.M.groundplate.SLDPRT

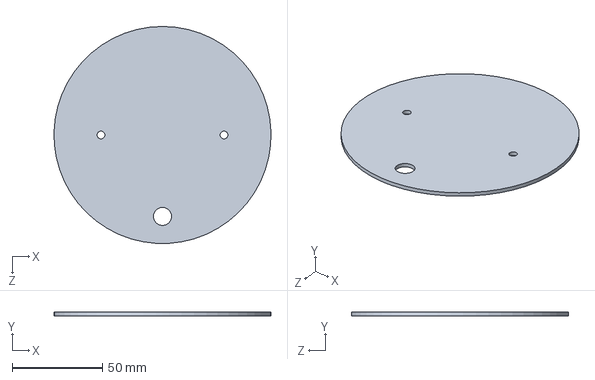
[picture p74: CAD file, 2020-09-22]
SolidWorks 3D models/shared parts ROVER2 and BASE2/Universal.M.groundplate.SLDPRT
119.9 x 2.00 x 120.0 mm
