PJ-Verweij/LowCostHighPrecisionPositioning---BASE2-ROVER2/SolidWorks 3D models/ROVER2/Rover.B.4x22_o-ring.SLDPRT

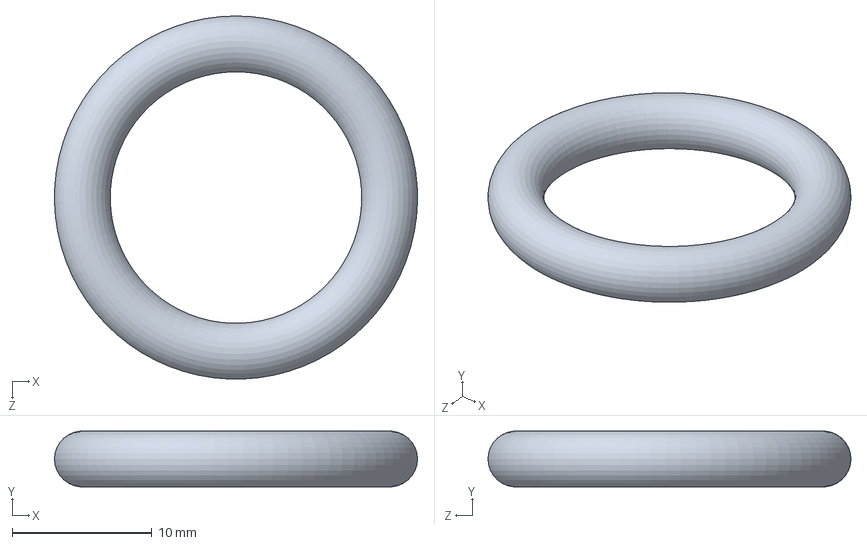
[picture p75: CAD file, 2020-09-22]
SolidWorks 3D models/ROVER2/Rover.B.4x22_o-ring.SLDPRT
26.0 x 3.98 x 26.0 mm
