PJ-Verweij/LowCostHighPrecisionPositioning---BASE2-ROVER2/SolidWorks 3D models/ROVER2/Rover.M.Foamblockholder.SLDPRT

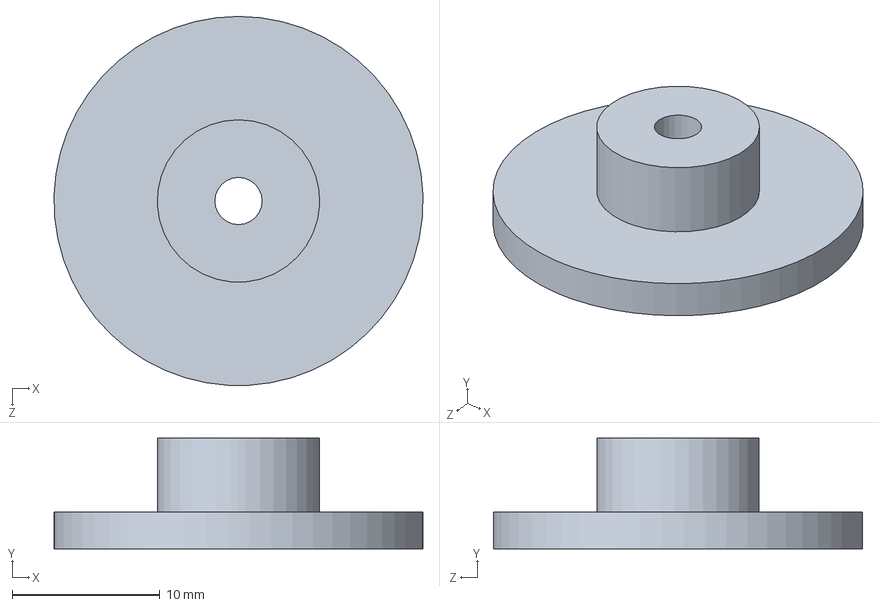
[picture p76: CAD file, 2020-09-22]
SolidWorks 3D models/ROVER2/Rover.M.Foamblockholder.SLDPRT
25.0 x 7.50 x 25.0 mm
