PJ-Verweij/LowCostHighPrecisionPositioning---BASE2-ROVER2/SolidWorks 3D models/BASE2/Base.B.M16_powerconnector_Applamp.SLDPRT

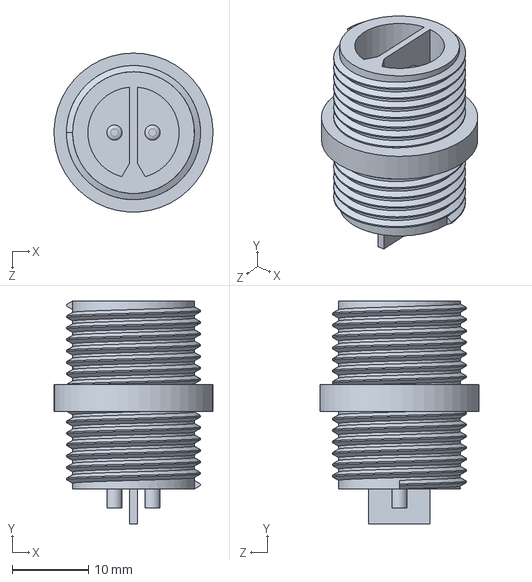
[picture p77: CAD file, 2020-09-22]
SolidWorks 3D models/BASE2/Base.B.M16_powerconnector_Applamp.SLDPRT
20.9 x 29.3 x 20.9 mm
