PJ-Verweij/LowCostHighPrecisionPositioning---BASE2-ROVER2/SolidWorks 3D models/ROVER2/Rover.M.Cap_rubber.SLDPRT

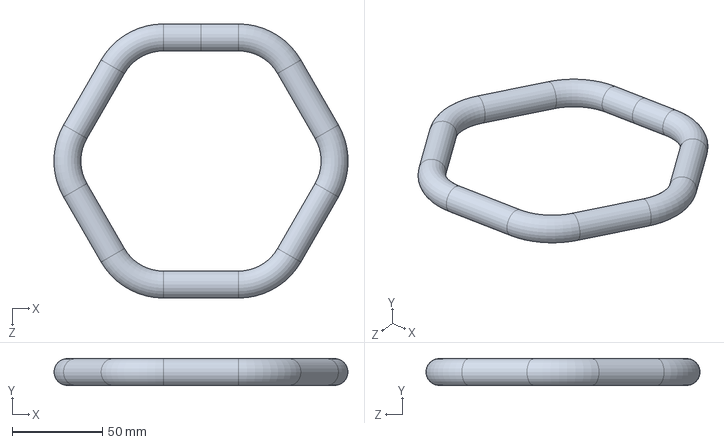
[picture p78: CAD file, 2020-09-22]
SolidWorks 3D models/ROVER2/Rover.M.Cap_rubber.SLDPRT
163.2 x 15.0 x 152.2 mm
