PJ-Verweij/LowCostHighPrecisionPositioning---BASE2-ROVER2/SolidWorks 3D models/BASE2/Base.M.housing.SLDPRT

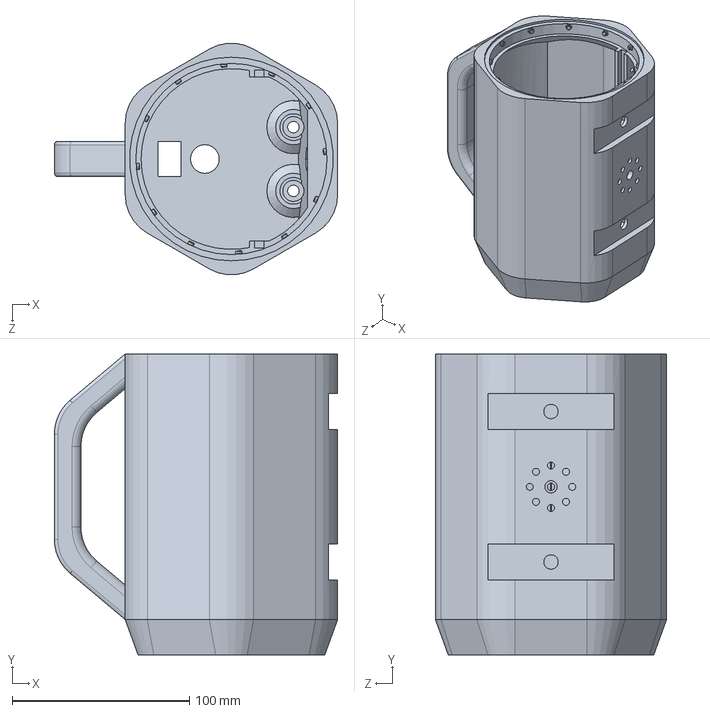
[picture p79: CAD file, 2020-09-22]
SolidWorks 3D models/BASE2/Base.M.housing.SLDPRT
160.0 x 170.0 x 130.6 mm
