PJ-Verweij/LowCostHighPrecisionPositioning---BASE2-ROVER2/SolidWorks 3D models/ROVER2/Rover.M.Plug.SLDPRT

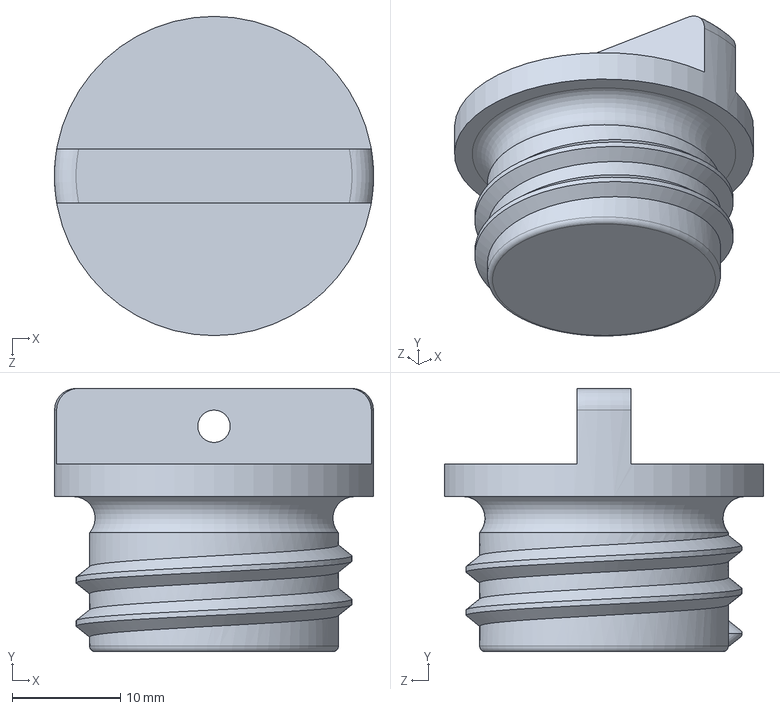
[picture p80: CAD file, 2020-09-22]
SolidWorks 3D models/ROVER2/Rover.M.Plug.SLDPRT
29.5 x 24.3 x 29.5 mm
