PJ-Verweij/LowCostHighPrecisionPositioning---BASE2-ROVER2/SolidWorks 3D models/BASE2/Base.M.electronics_sled_upperpart.SLDPRT

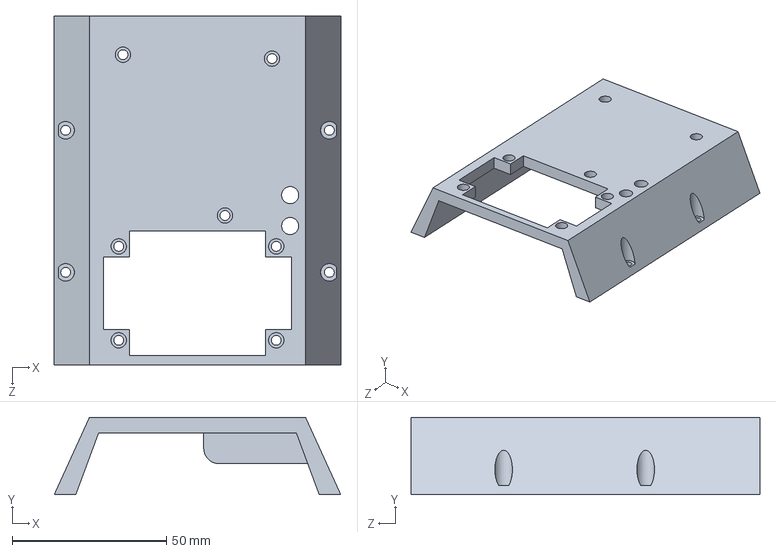
[picture p81: CAD file, 2020-09-22]
SolidWorks 3D models/BASE2/Base.M.electronics_sled_upperpart.SLDPRT
92.8 x 25.0 x 113.0 mm
