PJ-Verweij/LowCostHighPrecisionPositioning---BASE2-ROVER2/SolidWorks 3D models/ROVER2/Rover.M.BatteryLid.SLDPRT

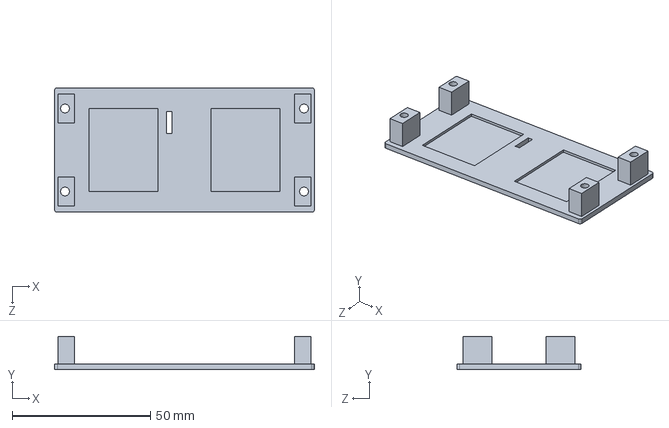
[picture p82: CAD file, 2020-09-22]
SolidWorks 3D models/ROVER2/Rover.M.BatteryLid.SLDPRT
94.0 x 12.0 x 45.0 mm
