PJ-Verweij/LowCostHighPrecisionPositioning---BASE2-ROVER2/SolidWorks 3D models/BASE2/Base.B.18650x4_holder.SLDPRT

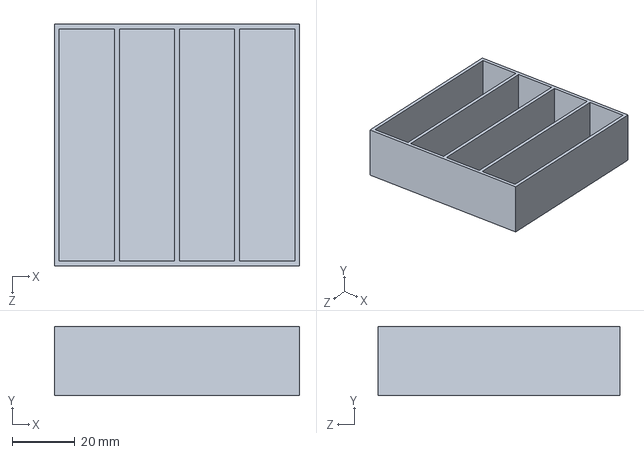
[picture p83: CAD file, 2020-09-22]
SolidWorks 3D models/BASE2/Base.B.18650x4_holder.SLDPRT
78.0 x 22.0 x 77.0 mm
