PJ-Verweij/LowCostHighPrecisionPositioning---BASE2-ROVER2/SolidWorks 3D models/ROVER2/Rover.B.3x118_o-ring.SLDPRT

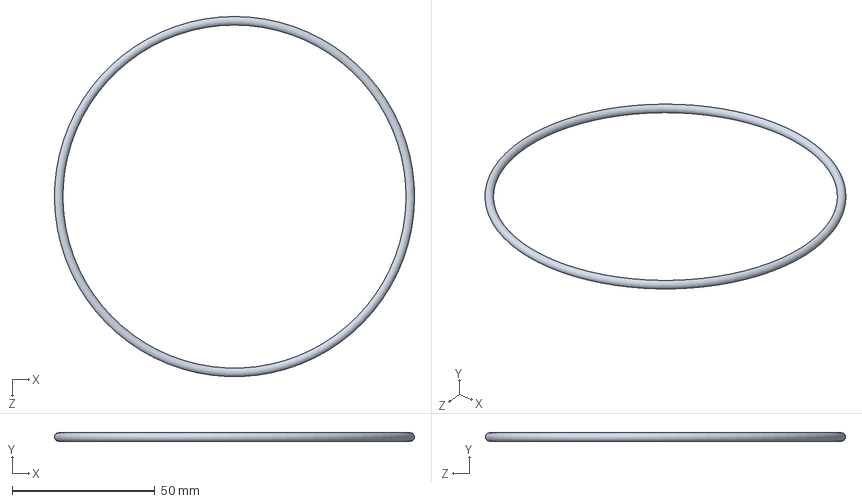
[picture p84: CAD file, 2020-09-22]
SolidWorks 3D models/ROVER2/Rover.B.3x118_o-ring.SLDPRT
126.0 x 3.00 x 125.9 mm
