PJ-Verweij/LowCostHighPrecisionPositioning---BASE2-ROVER2/SolidWorks 3D models/BASE2/Base.B.Square_Tube_Cap.SLDPRT

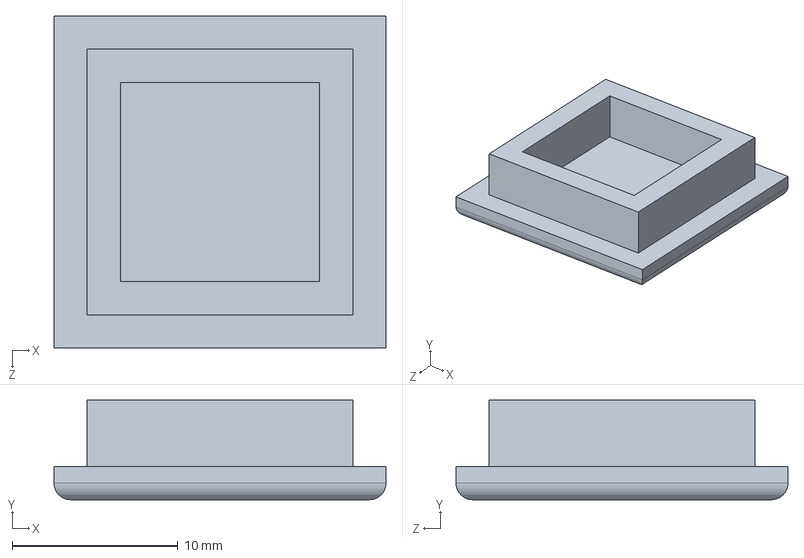
[picture p85: CAD file, 2020-09-22]
SolidWorks 3D models/BASE2/Base.B.Square_Tube_Cap.SLDPRT
20.0 x 6.00 x 20.0 mm
