PJ-Verweij/LowCostHighPrecisionPositioning---BASE2-ROVER2/SolidWorks 3D models/BASE2/Base.B.SMA_bulkhead.SLDPRT

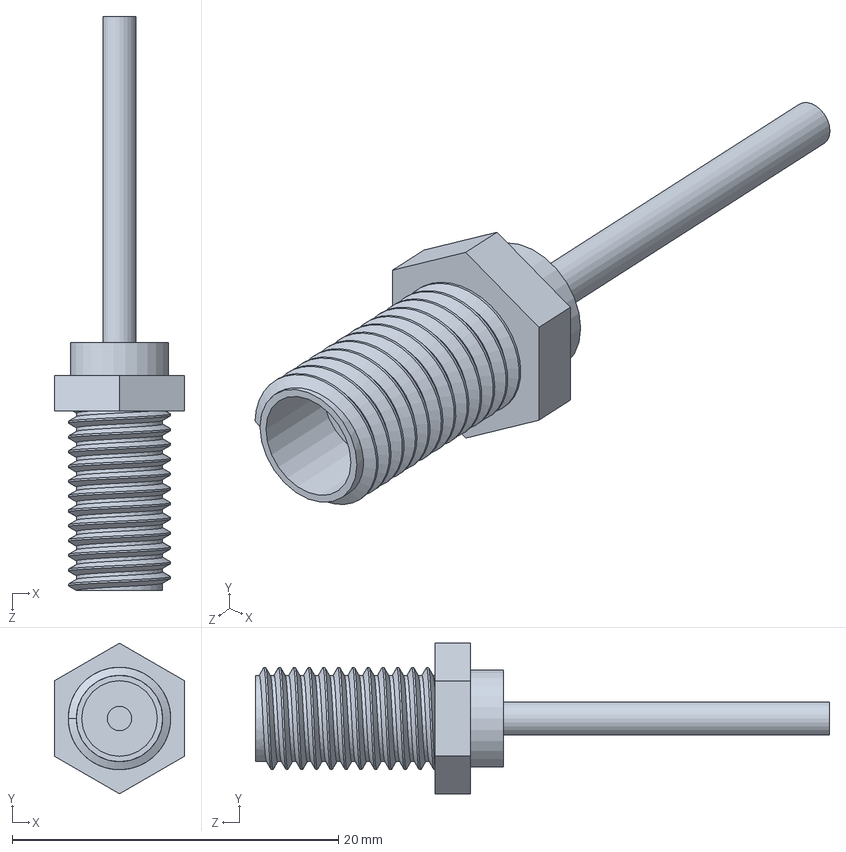
[picture p86: CAD file, 2020-09-22]
SolidWorks 3D models/BASE2/Base.B.SMA_bulkhead.SLDPRT
8.00 x 9.24 x 35.2 mm
