PJ-Verweij/LowCostHighPrecisionPositioning---BASE2-ROVER2/SolidWorks 3D models/BASE2/Base.B.solarconnector_lip.SLDPRT

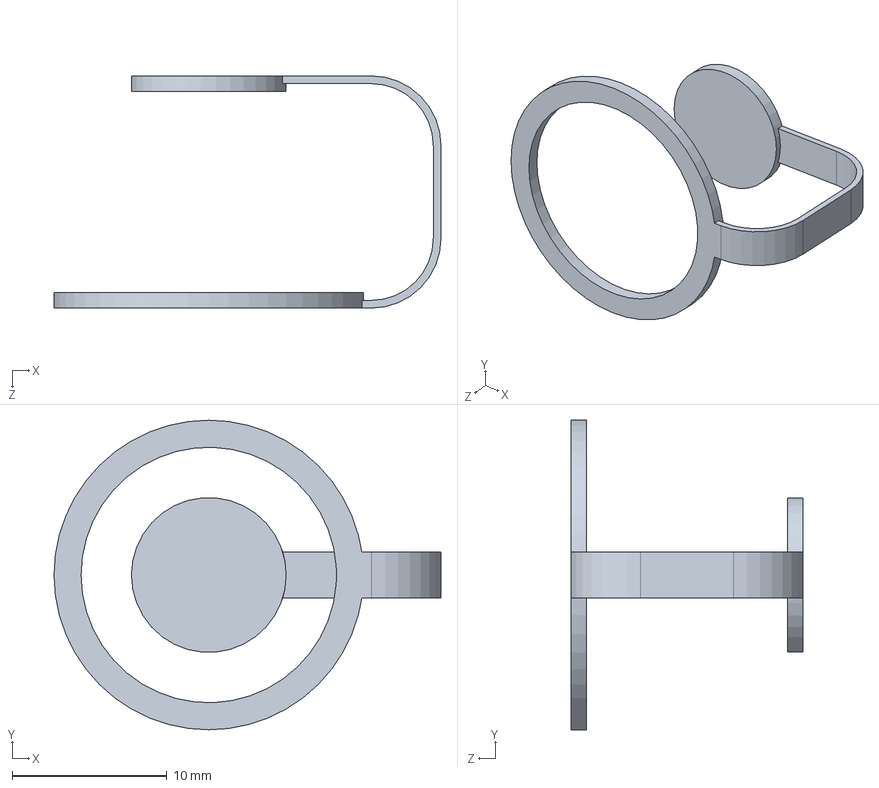
[picture p87: CAD file, 2020-09-22]
SolidWorks 3D models/BASE2/Base.B.solarconnector_lip.SLDPRT
25.0 x 20.0 x 15.0 mm
