PJ-Verweij/LowCostHighPrecisionPositioning---BASE2-ROVER2/SolidWorks 3D models/ROVER2/Rover.Plug.Assembly.SLDASM

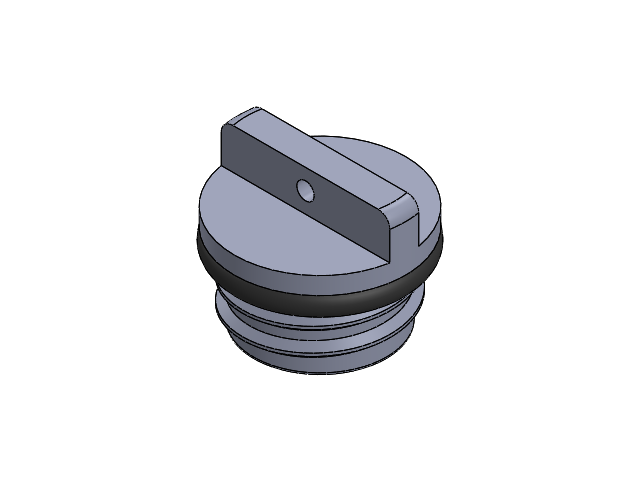
[picture p88: CAD file, 2020-09-22]
SolidWorks 3D models/ROVER2/Rover.Plug.Assembly.SLDASM
Rover.M.Plug
Rover.B.4x22_o-ring
